wickerwaka/Arcade-IGSPGM_MiSTer/rtl/jt12/ver/jt12_mmr/verify_sorted.csv

0 | 0 0 | b | 69 | 1 | 0b | 0 | 1e | 02 | a | 8 | 1 | 7 / 0 | 0aa | 5 | 0 | 0 | 1 | 2
0 | 1 6 | 8 | 5e | 2 | 12 | 1 | 01 | 1a | 9 | 9 | 0 | 3 / 0 | 0d4 | 1 | 7 | 0 | 3 | 1
0 | 2 4 | 7 | 54 | 2 | 0d | 0 | 1e | 1e | 0 | f | 1 | 6 / 0 | 0ac | 0 | 5 | 2 | 3 | 2
0 | 4 6 | d | 76 | 3 | 06 | 0 | 17 | 03 | 9 | 5 | 1 | 0 / 0 | 0f2 | 2 | 4 | 2 | 2 | 3
0 | 5 7 | 7 | 5a | 3 | 1b | 0 | 0a | 1b | b | 1 | 1 | 4 / 0 | 01b | 3 | 3 | 1 | 1 | 5
0 | 6 5 | 6 | 2e | 2 | 14 | 0 | 1c | 1a | e | b | 1 | 3 / 0 | 010 | 7 | 7 | 3 | 3 | 5
1 | 0 7 | 9 | 63 | 2 | 14 | 1 | 0b | 0a | f | 1 | 0 | 4 / 0 | 0aa | 5 | 0 | 0 | 1 | 2
1 | 1 4 | 3 | 33 | 1 | 11 | 1 | 16 | 1a | b | 3 | 0 | 5 / 0 | 0d4 | 1 | 7 | 0 | 3 | 1
1 | 2 6 | 1 | 1f | 0 | 0e | 1 | 0f | 1b | 0 | 5 | 0 | 4 / 0 | 0ac | 0 | 5 | 2 | 3 | 2
1 | 4 2 | f | 49 | 0 | 02 | 0 | 18 | 09 | e | f | 0 | 3 / 0 | 0f2 | 2 | 4 | 2 | 2 | 3
1 | 5 4 | a | 1a | 2 | 14 | 1 | 1c | 11 | f | 7 | 1 | 2 / 0 | 01b | 3 | 3 | 1 | 1 | 5
1 | 6 3 | c | 66 | 1 | 01 | 1 | 0a | 06 | 0 | 0 | 0 | 5 / 0 | 010 | 7 | 7 | 3 | 3 | 5
2 | 0 2 | 9 | 32 | 1 | 01 | 0 | 0c | 05 | e | 9 | 1 | 6 / 0 | 0aa | 5 | 0 | 0 | 1 | 2
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
