wickerwaka/Arcade-IGSPGM_MiSTer/rtl/jt10_auto_ss.sv

///////////////////////////////////////////
// MODULE jt12_dout
module jt12_dout (
    // input             rst_n,
    input               clk,                      // CPU clock
    input               flag_A,
    input               flag_B,
    input               busy,
    input        [ 5:0] adpcma_flags,
    input               adpcmb_flag,
    input        [ 7:0] psg_dout,
    input        [ 1:0] addr,
    output reg   [ 7:0] dout,
    input               auto_ss_rd,
    input               auto_ss_wr,
    input        [31:0] auto_ss_data_in,
    input        [ 7:0] auto_ss_device_idx,
    input        [15:0] auto_ss_state_idx,
    input        [ 7:0] auto_ss_base_device_idx,
    output logic [31:0] auto_ss_data_out,
    output logic        auto_ss_ack

);
  wire device_match = (auto_ss_device_idx == auto_ss_base_device_idx);

  genvar auto_ss_idx;


  parameter use_ssg = 0, use_adpcm = 0;

  always @(posedge clk) begin
    begin
      casez (addr)
        2'b00: dout <= {busy, 5'd0, flag_B, flag_A};  // YM2203
        2'b01: dout <= (use_ssg == 1) ? psg_dout : {busy, 5'd0, flag_B, flag_A};
        2'b1?:
        dout <= (use_adpcm == 1) ? {adpcmb_flag, 1'b0, adpcma_flags} : {busy, 5'd0, flag_B, flag_A};
      endcase
    end
    if (auto_ss_wr && device_match) begin
      case (auto_ss_state_idx)
        0: begin
          dout <= auto_ss_data_in[7:0];
        end
        default: begin
        end
      endcase
    end
  end


  always_comb begin
    auto_ss_data_out = 32'h0;
    auto_ss_ack      = 1'b0;
    if (auto_ss_rd && device_match) begin
      case (auto_ss_state_idx)
        0: begin
          auto_ss_data_out[8-1:0] = dout;
          auto_ss_ack             = 1'b1;
        end
        default: begin
        end
      endcase
    end
  end



endmodule


///////////////////////////////////////////
// MODULE jt12_div
module jt12_div (
    input               rst,
    input               clk,
    input               cen  /* synthesis direct_enable */,
    input        [ 1:0] div_setting,
    output reg          clk_en,                              // after prescaler
    output reg          clk_en_2,                            // cen divided by 2
    output reg          clk_en_ssg,
    output reg          clk_en_666,                          // 666 kHz
    output reg          clk_en_111,                          // 111 kHz
    output reg          clk_en_55,
    input               auto_ss_rd,
    input               auto_ss_wr,
    input        [31:0] auto_ss_data_in,
    input        [ 7:0] auto_ss_device_idx,
    input        [15:0] auto_ss_state_idx,
    input        [ 7:0] auto_ss_base_device_idx,
    output logic [31:0] auto_ss_data_out,
    output logic        auto_ss_ack
    //  55 kHz
);
  wire device_match = (auto_ss_device_idx == auto_ss_base_device_idx);

  genvar auto_ss_idx;


  parameter use_ssg = 0;

  reg [3:0] opn_pres, opn_cnt = 4'd0;
  reg [2:0] ssg_pres, ssg_cnt = 3'd0;
  reg [4:0] adpcm_cnt666 = 5'd0;
  reg [2:0] adpcm_cnt111 = 3'd0, adpcm_cnt55 = 3'd0;
  reg cen_int, cen_ssg_int, cen_adpcm_int, cen_adpcm3_int;

  // prescaler values for FM
  // reset: 1/3
  // sel1/sel2
  //    0 0    1/3
  //    0 1    1/2
  //    1 0    1/6  
  //    1 1    1/2
  //
  // According to YM2608 document
  //                  FM      SSG   div[1:0]
  // reset value     1/6      1/4    10
  // 2D              1/6      1/4    10   | 10
  // 2D,2E           1/3      1/2    11   | 01
  // 2F              1/2      1/1    00   & 00
  //  

  always @(*) begin
    casez (div_setting)
      2'b0?: begin  // FM 1/2 - SSG 1/1
        opn_pres = 4'd2 - 4'd1;
        ssg_pres = 3'd0;
      end
      2'b10: begin  // FM 1/6 - SSG 1/4 (reset value. Fixed for YM2610)
        opn_pres = 4'd6 - 4'd1;
        ssg_pres = 3'd3;
      end
      2'b11: begin  // FM 1/3 - SSG 1/2
        opn_pres = 4'd3 - 4'd1;
        ssg_pres = 3'd1;
      end
    endcase  // div_setting
  end



  reg       cen_55_int;
  reg [1:0] div2 = 2'b0;

  always @(negedge clk) begin
    begin
      cen_int        <= opn_cnt == 4'd0;
      cen_ssg_int    <= ssg_cnt == 3'd0;
      cen_adpcm_int  <= adpcm_cnt666 == 5'd0;
      cen_adpcm3_int <= adpcm_cnt111 == 3'd0;
      cen_55_int     <= adpcm_cnt55 == 3'd0;

      clk_en         <= cen & cen_int;
      clk_en_2       <= cen && (div2 == 2'b00);
      clk_en_ssg     <= use_ssg ? (cen & cen_ssg_int) : 1'b0;
      clk_en_666     <= cen & cen_adpcm_int;
      clk_en_111     <= cen & cen_adpcm_int & cen_adpcm3_int;
      clk_en_55      <= cen & cen_adpcm_int & cen_adpcm3_int & cen_55_int;

    end
    if (auto_ss_wr && device_match) begin
      case (auto_ss_state_idx)
        0: begin
          cen_55_int     <= auto_ss_data_in[20];
          cen_adpcm3_int <= auto_ss_data_in[21];
          cen_adpcm_int  <= auto_ss_data_in[22];
          cen_int        <= auto_ss_data_in[23];
          cen_ssg_int    <= auto_ss_data_in[24];
          clk_en         <= auto_ss_data_in[25];
          clk_en_111     <= auto_ss_data_in[26];
          clk_en_2       <= auto_ss_data_in[27];
          clk_en_55      <= auto_ss_data_in[28];
          clk_en_666     <= auto_ss_data_in[29];
          clk_en_ssg     <= auto_ss_data_in[30];
        end
        default: begin
        end
      endcase
    end
  end



  // Div/2
  always @(posedge clk) begin

    if (cen) begin
      div2 <= div2 == 2'b10 ? 2'b00 : (div2 + 2'b01);
    end
    if (auto_ss_wr && device_match) begin
      case (auto_ss_state_idx)
        0: begin
          div2 <= auto_ss_data_in[19:18];
        end
        default: begin
        end
      endcase
    end
  end



  // OPN
  always @(posedge clk) begin

    if (cen) begin
      if (opn_cnt == opn_pres) begin
        opn_cnt <= 4'd0;
      end else opn_cnt <= opn_cnt + 4'd1;
    end
    if (auto_ss_wr && device_match) begin
      case (auto_ss_state_idx)
        0: begin
          opn_cnt <= auto_ss_data_in[8:5];
        end
        default: begin
        end
      endcase
    end
  end



  // SSG
  always @(posedge clk) begin

    if (cen) begin
      if (ssg_cnt == ssg_pres) begin
        ssg_cnt <= 3'd0;
      end else ssg_cnt <= ssg_cnt + 3'd1;
    end
    if (auto_ss_wr && device_match) begin
      case (auto_ss_state_idx)
        0: begin
          ssg_cnt <= auto_ss_data_in[11:9];
        end
        default: begin
        end
      endcase
    end
  end



  // ADPCM-A
  always @(posedge clk) begin

    if (cen) begin
      adpcm_cnt666 <= adpcm_cnt666 == 5'd11 ? 5'd0 : adpcm_cnt666 + 5'd1;
      if (adpcm_cnt666 == 5'd0) begin
        adpcm_cnt111 <= adpcm_cnt111 == 3'd5 ? 3'd0 : adpcm_cnt111 + 3'd1;
        if (adpcm_cnt111 == 3'd0) adpcm_cnt55 <= adpcm_cnt55 == 3'd1 ? 3'd0 : adpcm_cnt55 + 3'd1;
      end
    end
    if (auto_ss_wr && device_match) begin
      case (auto_ss_state_idx)
        0: begin
          adpcm_cnt666 <= auto_ss_data_in[4:0];
          adpcm_cnt111 <= auto_ss_data_in[14:12];
          adpcm_cnt55  <= auto_ss_data_in[17:15];
        end
        default: begin
        end
      endcase
    end
  end


  always_comb begin
    auto_ss_data_out = 32'h0;
    auto_ss_ack      = 1'b0;
    if (auto_ss_rd && device_match) begin
      case (auto_ss_state_idx)
        0: begin
          auto_ss_data_out[30:0] = {
            clk_en_ssg,
            clk_en_666,
            clk_en_55,
            clk_en_2,
            clk_en_111,
            clk_en,
            cen_ssg_int,
            cen_int,
            cen_adpcm_int,
            cen_adpcm3_int,
            cen_55_int,
            div2,
            adpcm_cnt55,
            adpcm_cnt111,
            ssg_cnt,
            opn_cnt,
            adpcm_cnt666
          };
          auto_ss_ack = 1'b1;
        end
        default: begin
        end
      endcase
    end
  end



endmodule


///////////////////////////////////////////
// MODULE jt12_sumch
module jt12_sumch (
    input      [4:0] chin,
    output reg [4:0] chout
);

  parameter num_ch = 6;

  reg [2:0] aux;

  always @(*) begin
    aux = chin[2:0] + 3'd1;
    if (num_ch == 6) begin
      chout[2:0] = aux[1:0] == 2'b11 ? aux + 3'd1 : aux;
      chout[4:3] = chin[2:0] == 3'd6 ? chin[4:3] + 2'd1 : chin[4:3];  // next operator
    end else begin  // 3 channels
      chout[2:0] = aux[1:0] == 2'b11 ? 3'd0 : aux;
      chout[4:3] = chin[2:0] == 3'd2 ? chin[4:3] + 2'd1 : chin[4:3];  // next operator
    end
  end

endmodule


///////////////////////////////////////////
// MODULE jt12_sh_rst
module jt12_sh_rst #(
    parameter width  = 5,
              stages = 32,
              rstval = 1'b0
) (
    input                    rst,
    input                    clk,
    input                    clk_en  /* synthesis direct_enable */,
    input        [width-1:0] din,
    output       [width-1:0] drop,
    input                    auto_ss_rd,
    input                    auto_ss_wr,
    input        [     31:0] auto_ss_data_in,
    input        [      7:0] auto_ss_device_idx,
    input        [     15:0] auto_ss_state_idx,
    input        [      7:0] auto_ss_base_device_idx,
    output logic [     31:0] auto_ss_data_out,
    output logic             auto_ss_ack


);
  wire device_match = (auto_ss_device_idx == auto_ss_base_device_idx);

  genvar auto_ss_idx;


  reg  [stages-1:0] bits                                    [width-1:0];
  wire [ width-1:0] din_mx = rst ? {width{rstval[0]}} : din;

  always @(posedge clk) begin
    begin
      if (clk_en) begin
        for (int i = 0; i < width; i = i + 1) begin
          bits[i] <= {bits[i][stages-2:0], din_mx[i]};
        end
      end
    end
    if (auto_ss_wr && device_match) begin
      if (auto_ss_state_idx < (width)) begin
        bits[auto_ss_state_idx] <= auto_ss_data_in[stages-1:0];
      end
    end
  end


  always_comb begin
    auto_ss_data_out = 32'h0;
    auto_ss_ack      = 1'b0;
    if (auto_ss_rd && device_match) begin
      if (auto_ss_state_idx < (width)) begin
        auto_ss_data_out[stages-1:0] = bits[auto_ss_state_idx];
        auto_ss_ack                  = 1'b1;
      end
    end
  end



  genvar i;
  generate
    for (i = 0; i < width; i = i + 1) begin : bit_shifter
      assign drop[i] = bits[i][stages-1];
    end
  endgenerate

endmodule


///////////////////////////////////////////
// MODULE jt12_kon
module jt12_kon (
    input       rst,
    input       clk,
    input       clk_en  /* synthesis direct_enable */,
    input [3:0] keyon_op,
    input [2:0] keyon_ch,
    input [1:0] next_op,
    input [2:0] next_ch,
    input       up_keyon,
    input       csm,
    // input            flag_A,
    input       overflow_A,

    output reg          keyon_I,
    input               auto_ss_rd,
    input               auto_ss_wr,
    input        [31:0] auto_ss_data_in,
    input        [ 7:0] auto_ss_device_idx,
    input        [15:0] auto_ss_state_idx,
    input        [ 7:0] auto_ss_base_device_idx,
    output logic [31:0] auto_ss_data_out,
    output logic        auto_ss_ack

);
  assign auto_ss_ack = auto_ss_local_ack | auto_ss_u_konch0_ack | auto_ss_u_konch1_ack | auto_ss_u_konch2_ack | auto_ss_u_konch3_ack;

  assign auto_ss_data_out = auto_ss_local_data_out | auto_ss_u_konch0_data_out | auto_ss_u_konch1_data_out | auto_ss_u_konch2_data_out | auto_ss_u_konch3_data_out;

  logic        auto_ss_local_ack;

  logic [31:0] auto_ss_local_data_out;

  wire         auto_ss_u_konch3_ack;

  wire  [31:0] auto_ss_u_konch3_data_out;

  wire         auto_ss_u_konch2_ack;

  wire  [31:0] auto_ss_u_konch2_data_out;

  wire         auto_ss_u_konch1_ack;

  wire  [31:0] auto_ss_u_konch1_data_out;

  wire         auto_ss_u_konch0_ack;

  wire  [31:0] auto_ss_u_konch0_data_out;

  wire         device_match = (auto_ss_device_idx == auto_ss_base_device_idx);

  genvar auto_ss_idx;


  parameter num_ch = 6;

  wire       csr_out;

  reg        overflow2;
  reg  [4:0] overflow_cycle;
  reg        up_keyon_reg;
  reg  [3:0] tkeyon_op;
  reg  [2:0] tkeyon_ch;


  generate
    if (num_ch == 6) begin
      // capture overflow signal so it lasts long enough
      always @(posedge clk) begin
        if (clk_en) begin
          if (overflow_A) begin
            overflow2      <= 1'b1;
            overflow_cycle <= {next_op, next_ch};
          end else begin
            if (overflow_cycle == {next_op, next_ch}) overflow2 <= 1'b0;
          end
        end
        if (auto_ss_wr && device_match) begin
          case (auto_ss_state_idx)
            0: begin
              overflow_cycle <= auto_ss_data_in[4:0];
              overflow2      <= auto_ss_data_in[12];
            end
            default: begin
            end
          endcase
        end
      end



      always @(posedge clk) begin
        if (clk_en) keyon_I <= (csm && next_ch == 3'd2 && overflow2) || csr_out;
        if (auto_ss_wr && device_match) begin
          case (auto_ss_state_idx)
            0: begin
              keyon_I <= auto_ss_data_in[15];
              keyon_I <= auto_ss_data_in[15];
            end
            default: begin
            end
          endcase
        end
      end



      wire key_upnow;

      assign key_upnow = up_keyon_reg && (tkeyon_ch == next_ch) && (next_op == 2'd3);

      always @(posedge clk) begin
        if (clk_en) begin
          if (rst) up_keyon_reg <= 1'b0;
          if (up_keyon) begin
            up_keyon_reg <= 1'b1;
            tkeyon_op    <= keyon_op;
            tkeyon_ch    <= keyon_ch;
          end else if (key_upnow) up_keyon_reg <= 1'b0;
        end
        if (auto_ss_wr && device_match) begin
          case (auto_ss_state_idx)
            0: begin
              tkeyon_op    <= auto_ss_data_in[8:5];
              tkeyon_ch    <= auto_ss_data_in[11:9];
              up_keyon_reg <= auto_ss_data_in[14];
            end
            default: begin
            end
          endcase
        end
      end




      wire middle1;
      wire middle2;
      wire middle3;
      wire din = key_upnow ? tkeyon_op[3] : csr_out;
      wire mid_din2 = key_upnow ? tkeyon_op[1] : middle1;
      wire mid_din3 = key_upnow ? tkeyon_op[2] : middle2;
      wire mid_din4 = key_upnow ? tkeyon_op[0] : middle3;

      jt12_sh_rst #(
          .width (1),
          .stages(6),
          .rstval(1'b0)
      ) u_konch0 (
          .clk                    (clk),
          .clk_en                 (clk_en),
          .rst                    (rst),
          .din                    (din),
          .drop                   (middle1),
          .auto_ss_rd             (auto_ss_rd),
          .auto_ss_wr             (auto_ss_wr),
          .auto_ss_data_in        (auto_ss_data_in),
          .auto_ss_device_idx     (auto_ss_device_idx),
          .auto_ss_state_idx      (auto_ss_state_idx),
          .auto_ss_base_device_idx(auto_ss_base_device_idx + 1),
          .auto_ss_data_out       (auto_ss_u_konch0_data_out),
          .auto_ss_ack            (auto_ss_u_konch0_ack)

      );

      jt12_sh_rst #(
          .width (1),
          .stages(6),
          .rstval(1'b0)
      ) u_konch1 (
          .clk                    (clk),
          .clk_en                 (clk_en),
          .rst                    (rst),
          .din                    (mid_din2),
          .drop                   (middle2),
          .auto_ss_rd             (auto_ss_rd),
          .auto_ss_wr             (auto_ss_wr),
          .auto_ss_data_in        (auto_ss_data_in),
          .auto_ss_device_idx     (auto_ss_device_idx),
          .auto_ss_state_idx      (auto_ss_state_idx),
          .auto_ss_base_device_idx(auto_ss_base_device_idx + 2),
          .auto_ss_data_out       (auto_ss_u_konch1_data_out),
          .auto_ss_ack            (auto_ss_u_konch1_ack)

      );

      jt12_sh_rst #(
          .width (1),
          .stages(6),
          .rstval(1'b0)
      ) u_konch2 (
          .clk                    (clk),
          .clk_en                 (clk_en),
          .rst                    (rst),
          .din                    (mid_din3),
          .drop                   (middle3),
          .auto_ss_rd             (auto_ss_rd),
          .auto_ss_wr             (auto_ss_wr),
          .auto_ss_data_in        (auto_ss_data_in),
          .auto_ss_device_idx     (auto_ss_device_idx),
          .auto_ss_state_idx      (auto_ss_state_idx),
          .auto_ss_base_device_idx(auto_ss_base_device_idx + 3),
          .auto_ss_data_out       (auto_ss_u_konch2_data_out),
          .auto_ss_ack            (auto_ss_u_konch2_ack)

      );

      jt12_sh_rst #(
          .width (1),
          .stages(6),
          .rstval(1'b0)
      ) u_konch3 (
          .clk                    (clk),
          .clk_en                 (clk_en),
          .rst                    (rst),
          .din                    (mid_din4),
          .drop                   (csr_out),
          .auto_ss_rd             (auto_ss_rd),
          .auto_ss_wr             (auto_ss_wr),
          .auto_ss_data_in        (auto_ss_data_in),
          .auto_ss_device_idx     (auto_ss_device_idx),
          .auto_ss_state_idx      (auto_ss_state_idx),
          .auto_ss_base_device_idx(auto_ss_base_device_idx + 4),
          .auto_ss_data_out       (auto_ss_u_konch3_data_out),
          .auto_ss_ack            (auto_ss_u_konch3_ack)

      );
    end else begin  // 3 channels
      reg       din;
      reg [3:0] next_op_hot;

      always @(*) begin
        case (next_op)
          2'd0: next_op_hot = 4'b0001;  // S1
          2'd1: next_op_hot = 4'b0100;  // S3
          2'd2: next_op_hot = 4'b0010;  // S2
          2'd3: next_op_hot = 4'b1000;  // S4
        endcase
        din = keyon_ch[1:0] == next_ch[1:0] && up_keyon ? |(keyon_op & next_op_hot) : csr_out;
      end

      always @(posedge clk) begin
        if (clk_en) keyon_I <= csr_out;
        if (auto_ss_wr && device_match) begin
          case (auto_ss_state_idx)
            0: begin
              keyon_I <= auto_ss_data_in[15];
              keyon_I <= auto_ss_data_in[15];
            end
            default: begin
            end
          endcase
        end
      end


      always_comb begin
        auto_ss_local_data_out = 32'h0;
        auto_ss_local_ack      = 1'b0;
        if (auto_ss_rd && device_match) begin
          case (auto_ss_state_idx)
            0: begin
              auto_ss_local_data_out[15:0] = {
                keyon_I, keyon_I, up_keyon_reg, overflow2, tkeyon_ch, tkeyon_op, overflow_cycle
              };
              auto_ss_local_ack = 1'b1;
            end
            default: begin
            end
          endcase
        end
      end

      // No CSM for YM2203

      jt12_sh_rst #(
          .width (1),
          .stages(12),
          .rstval(1'b0)
      ) u_konch1 (
          .clk                    (clk),
          .clk_en                 (clk_en),
          .rst                    (rst),
          .din                    (din),
          .drop                   (csr_out),
          .auto_ss_rd             (auto_ss_rd),
          .auto_ss_wr             (auto_ss_wr),
          .auto_ss_data_in        (auto_ss_data_in),
          .auto_ss_device_idx     (auto_ss_device_idx),
          .auto_ss_state_idx      (auto_ss_state_idx),
          .auto_ss_base_device_idx(auto_ss_base_device_idx + 5),
          .auto_ss_data_out       (auto_ss_u_konch1_data_out),
          .auto_ss_ack            (auto_ss_u_konch1_ack)

      );
    end
  endgenerate


endmodule


///////////////////////////////////////////
// MODULE jt12_mod
module jt12_mod (
    input s1_enters,
    input s2_enters,
    input s3_enters,
    input s4_enters,

    input [2:0] alg_I,

    output reg xuse_prevprev1,
    output reg xuse_internal,
    output reg yuse_internal,
    output reg xuse_prev2,
    output reg yuse_prev1,
    output reg yuse_prev2
);

  parameter num_ch = 6;

  reg [7:0] alg_hot;

  always @(*) begin
    case (alg_I)
      3'd0: alg_hot = 8'h1;  // D0
      3'd1: alg_hot = 8'h2;  // D1
      3'd2: alg_hot = 8'h4;  // D2
      3'd3: alg_hot = 8'h8;  // D3
      3'd4: alg_hot = 8'h10;  // D4
      3'd5: alg_hot = 8'h20;  // D5
      3'd6: alg_hot = 8'h40;  // D6
      3'd7: alg_hot = 8'h80;  // D7
    endcase
  end

  // prev2 cannot modulate with prevprev1 at the same time
  // x = prev2, prevprev1, internal_x
  // y = prev1, internal_y

  generate
    if (num_ch == 6) begin
      always @(*) begin
        xuse_prevprev1 = s1_enters | (s3_enters & alg_hot[5]);
        xuse_prev2 = (s3_enters & (|alg_hot[2:0])) | (s4_enters & alg_hot[3]);
        xuse_internal = s4_enters & alg_hot[2];
        yuse_internal = s4_enters & (|{alg_hot[4:3], alg_hot[1:0]});
        yuse_prev1 = s1_enters | (s3_enters&alg_hot[1]) |
                (s2_enters&(|{alg_hot[6:3],alg_hot[0]}) )|
                (s4_enters&(|{alg_hot[5],alg_hot[2]}));
        yuse_prev2 = 1'b0;  // unused for 6 channels
      end
    end else begin
      reg [2:0] xuse_s4, xuse_s3, xuse_s2, xuse_s1;
      reg [2:0] yuse_s4, yuse_s3, yuse_s2, yuse_s1;
      always @(*) begin  // 3 ch
        // S1
        {xuse_s1, yuse_s1} = {3'b001, 3'b100};
        // S2
        casez (1'b1)
          // S2 modulated by S1
          alg_hot[6], alg_hot[5], alg_hot[4], alg_hot[3], alg_hot[0]:
          {xuse_s2, yuse_s2} = {3'b000, 3'b100};  // prev1
          default: {xuse_s2, yuse_s2} = 6'd0;
        endcase
        // S3
        casez (1'b1)
          // S3 modulated by S1
          alg_hot[5]: {xuse_s3, yuse_s3} = {3'b000, 3'b100};  // prev1
          // S3 modulated by S2
          alg_hot[2], alg_hot[0]: {xuse_s3, yuse_s3} = {3'b000, 3'b010};  // prev2
          // S3 modulated by S2+S1
          alg_hot[1]: {xuse_s3, yuse_s3} = {3'b010, 3'b100};  // prev2 + prev1                   
          default: {xuse_s3, yuse_s3} = 6'd0;
        endcase
        // S4
        casez (1'b1)
          // S4 modulated by S1
          alg_hot[5]: {xuse_s4, yuse_s4} = {3'b000, 3'b100};  // prev1
          // S4 modulated by S3
          alg_hot[4], alg_hot[1], alg_hot[0]: {xuse_s4, yuse_s4} = {3'b100, 3'b000};  // prevprev1
          // S4 modulated by S3+S2
          alg_hot[3]: {xuse_s4, yuse_s4} = {3'b100, 3'b010};  // prevprev1+prev2                    
          // S4 modulated by S3+S1
          alg_hot[2]: {xuse_s4, yuse_s4} = {3'b100, 3'b100};  // prevprev1+prev1
          default: {xuse_s4, yuse_s4} = 6'd0;
        endcase
        case ({
          s4_enters, s3_enters, s2_enters, s1_enters
        })
          4'b1000: begin
            {xuse_prevprev1, xuse_prev2, xuse_internal} = xuse_s4;
            {yuse_prev1, yuse_prev2, yuse_internal}     = yuse_s4;
          end
          4'b0100: begin
            {xuse_prevprev1, xuse_prev2, xuse_internal} = xuse_s3;
            {yuse_prev1, yuse_prev2, yuse_internal}     = yuse_s3;
          end
          4'b0010: begin
            {xuse_prevprev1, xuse_prev2, xuse_internal} = xuse_s2;
            {yuse_prev1, yuse_prev2, yuse_internal}     = yuse_s2;
          end
          4'b0001: begin
            {xuse_prevprev1, xuse_prev2, xuse_internal} = xuse_s1;
            {yuse_prev1, yuse_prev2, yuse_internal}     = yuse_s1;
          end
          default: begin
            {xuse_prevprev1, xuse_prev2, xuse_internal} = 3'b0;
            {yuse_prev1, yuse_prev2, yuse_internal}     = 3'b0;
          end
        endcase
      end
    end
  endgenerate

  // Control signals for simulation: should be 2'b0 or 2'b1
  // wire [1:0] xusage = xuse_prevprev1+xuse_prev2+xuse_internal;
  // wire [1:0] yusage = yuse_prev1+yuse_internal;
  // 
  // always @(xusage,yusage)
  //     if( xusage>2'b1 || yusage>2'b1 ) begin
  //         $display("ERROR: x/y over use in jt12_mod");
  //         $finish;
  //     end

endmodule


///////////////////////////////////////////
// MODULE jt12_reg_ch
module jt12_reg_ch (
    input       rst,
    input       clk,
    input       cen,
    input [7:0] din,

    input [2:0] up_ch,
    input [5:0] latch_fnum,
    input       up_fnumlo,
    input       up_alg,
    input       up_pms,

    input        [ 2:0] ch,                       // next active channel
    output reg   [ 2:0] block,
    output reg   [10:0] fnum,
    output reg   [ 2:0] fb,
    output reg   [ 2:0] alg,
    output reg   [ 1:0] rl,
    output reg   [ 1:0] ams_IV,
    output reg   [ 2:0] pms,
    input               auto_ss_rd,
    input               auto_ss_wr,
    input        [31:0] auto_ss_data_in,
    input        [ 7:0] auto_ss_device_idx,
    input        [15:0] auto_ss_state_idx,
    input        [ 7:0] auto_ss_base_device_idx,
    output logic [31:0] auto_ss_data_out,
    output logic        auto_ss_ack

);
  wire device_match = (auto_ss_device_idx == auto_ss_base_device_idx);

  genvar auto_ss_idx;


  parameter NUM_CH = 6;
  localparam M = NUM_CH == 3 ? 2 : 3;

  reg [ 2:0] reg_block[0:NUM_CH-1];
  reg [10:0] reg_fnum [0:NUM_CH-1];
  reg [ 2:0] reg_fb   [0:NUM_CH-1];
  reg [ 2:0] reg_alg  [0:NUM_CH-1];
  reg [ 1:0] reg_rl   [0:NUM_CH-1];
  reg [ 1:0] reg_ams  [0:NUM_CH-1];
  reg [ 2:0] reg_pms  [0:NUM_CH-1];
  reg [ 2:0] ch_IV;

  wire [M-1:0] ch_sel, out_sel;

  function [M-1:0] chtr(input [2:0] chin);
    reg [2:0] aux;
    begin
      aux  = chin[M-1] ? {1'b0, chin[1:0]} + 3'd3 :  // upper channels
{1'b0, chin[1:0]};  // lower
      chtr = NUM_CH == 3 ? chin[M-1:0] : aux[M-1:0];

    end
  endfunction

  assign ch_sel  = chtr(up_ch);
  assign out_sel = chtr(ch);

  integer i;
  /* verilator lint_off WIDTHEXPAND */
  always @* begin
    ch_IV = ch;
    if (NUM_CH == 6)
      case (out_sel)
        0: ch_IV = 3;
        1: ch_IV = 4;
        2: ch_IV = 5;
        3: ch_IV = 0;
        4: ch_IV = 1;
        5: ch_IV = 2;
        default: ch_IV = 0;
      endcase
  end
  /* verilator lint_on WIDTHEXPAND */

  always @(posedge clk) begin
    if (cen) begin
      block  <= reg_block[out_sel];
      fnum   <= reg_fnum[out_sel];
      fb     <= reg_fb[out_sel];
      alg    <= reg_alg[out_sel];
      rl     <= reg_rl[out_sel];
      ams_IV <= reg_ams[ch_IV[M-1:0]];
      pms    <= reg_pms[out_sel];
      if (NUM_CH == 3) rl <= 3;  // YM2203 has no stereo output
    end
    if (auto_ss_wr && device_match) begin
      case (auto_ss_state_idx)
        0: begin
          fnum   <= auto_ss_data_in[10:0];
          alg    <= auto_ss_data_in[13:11];
          block  <= auto_ss_data_in[16:14];
          fb     <= auto_ss_data_in[19:17];
          pms    <= auto_ss_data_in[22:20];
          ams_IV <= auto_ss_data_in[24:23];
          rl     <= auto_ss_data_in[26:25];
        end
        default: begin
        end
      endcase
    end
  end



  always @(posedge clk, posedge rst) begin
    if (rst)
      for (i = 0; i < NUM_CH; i = i + 1) begin
        reg_block[i] <= 0;
        reg_fnum[i]  <= 0;
        reg_fb[i]    <= 0;
        reg_alg[i]   <= 0;
        reg_rl[i]    <= 3;
        reg_ams[i]   <= 0;
        reg_pms[i]   <= 0;
      end
    else if (auto_ss_wr && device_match) begin
      if (auto_ss_state_idx >= (1) && auto_ss_state_idx < (NUM_CH + 1)) begin
        reg_alg[auto_ss_state_idx-1] <= auto_ss_data_in[2:0];
      end
      if (auto_ss_state_idx >= (NUM_CH + 1) && auto_ss_state_idx < (2 * NUM_CH + 1)) begin
        reg_ams[-NUM_CH+auto_ss_state_idx-1] <= auto_ss_data_in[1:0];
      end
      if (auto_ss_state_idx >= (2 * NUM_CH + 1) && auto_ss_state_idx < (3 * NUM_CH + 1)) begin
        reg_block[-2*NUM_CH+auto_ss_state_idx-1] <= auto_ss_data_in[2:0];
      end
      if (auto_ss_state_idx >= (3 * NUM_CH + 1) && auto_ss_state_idx < (4 * NUM_CH + 1)) begin
        reg_fb[-3*NUM_CH+auto_ss_state_idx-1] <= auto_ss_data_in[2:0];
      end
      if (auto_ss_state_idx >= (4 * NUM_CH + 1) && auto_ss_state_idx < (5 * NUM_CH + 1)) begin
        reg_fnum[-4*NUM_CH+auto_ss_state_idx-1] <= auto_ss_data_in[10:0];
      end
      if (auto_ss_state_idx >= (5 * NUM_CH + 1) && auto_ss_state_idx < (6 * NUM_CH + 1)) begin
        reg_pms[-5*NUM_CH+auto_ss_state_idx-1] <= auto_ss_data_in[2:0];
      end
      if (auto_ss_state_idx >= (6 * NUM_CH + 1) && auto_ss_state_idx < (7 * NUM_CH + 1)) begin
        reg_rl[-6*NUM_CH+auto_ss_state_idx-1] <= auto_ss_data_in[1:0];
      end
    end else begin
      i = 0;  // prevents latch warning in Quartus
      if (up_fnumlo) {reg_block[ch_sel], reg_fnum[ch_sel]} <= {latch_fnum, din};
      if (up_alg) begin
        reg_fb[ch_sel]  <= din[5:3];
        reg_alg[ch_sel] <= din[2:0];
      end
      if (up_pms) begin
        reg_rl[ch_sel]  <= din[7:6];
        reg_ams[ch_sel] <= din[5:4];
        reg_pms[ch_sel] <= din[2:0];
      end
    end
  end
  always_comb begin
    auto_ss_data_out = 32'h0;
    auto_ss_ack      = 1'b0;
    if (auto_ss_rd && device_match) begin
      case (auto_ss_state_idx)
        0: begin
          auto_ss_data_out[26:0] = {rl, ams_IV, pms, fb, block, alg, fnum};
          auto_ss_ack            = 1'b1;
        end
        default: begin
          if (auto_ss_state_idx >= (1) && auto_ss_state_idx < (NUM_CH + 1)) begin
            auto_ss_data_out[3-1:0] = reg_alg[auto_ss_state_idx-1];
            auto_ss_ack             = 1'b1;
          end
          if (auto_ss_state_idx >= (NUM_CH + 1) && auto_ss_state_idx < (2 * NUM_CH + 1)) begin
            auto_ss_data_out[2-1:0] = reg_ams[-NUM_CH+auto_ss_state_idx-1];
            auto_ss_ack             = 1'b1;
          end
          if (auto_ss_state_idx >= (2 * NUM_CH + 1) && auto_ss_state_idx < (3 * NUM_CH + 1)) begin
            auto_ss_data_out[3-1:0] = reg_block[-2*NUM_CH+auto_ss_state_idx-1];
            auto_ss_ack             = 1'b1;
          end
          if (auto_ss_state_idx >= (3 * NUM_CH + 1) && auto_ss_state_idx < (4 * NUM_CH + 1)) begin
            auto_ss_data_out[3-1:0] = reg_fb[-3*NUM_CH+auto_ss_state_idx-1];
            auto_ss_ack             = 1'b1;
          end
          if (auto_ss_state_idx >= (4 * NUM_CH + 1) && auto_ss_state_idx < (5 * NUM_CH + 1)) begin
            auto_ss_data_out[11-1:0] = reg_fnum[-4*NUM_CH+auto_ss_state_idx-1];
            auto_ss_ack              = 1'b1;
          end
          if (auto_ss_state_idx >= (5 * NUM_CH + 1) && auto_ss_state_idx < (6 * NUM_CH + 1)) begin
            auto_ss_data_out[3-1:0] = reg_pms[-5*NUM_CH+auto_ss_state_idx-1];
            auto_ss_ack             = 1'b1;
          end
          if (auto_ss_state_idx >= (6 * NUM_CH + 1) && auto_ss_state_idx < (7 * NUM_CH + 1)) begin
            auto_ss_data_out[2-1:0] = reg_rl[-6*NUM_CH+auto_ss_state_idx-1];
            auto_ss_ack             = 1'b1;
          end
        end
      endcase
    end
  end



endmodule


///////////////////////////////////////////
// MODULE jt12_csr
module jt12_csr (  // Circular Shift Register + input mux
    input         rst,
    input         clk,
    input         clk_en  /* synthesis direct_enable */,
    input  [ 7:0] din,
    input  [43:0] shift_in,
    output [43:0] shift_out,

    input               up_tl,
    input               up_dt1,
    input               up_ks_ar,
    input               up_amen_dr,
    input               up_sr,
    input               up_sl_rr,
    input               up_ssgeg,
    input               update_op_I,
    input               update_op_II,
    input               update_op_IV,
    input               auto_ss_rd,
    input               auto_ss_wr,
    input        [31:0] auto_ss_data_in,
    input        [ 7:0] auto_ss_device_idx,
    input        [15:0] auto_ss_state_idx,
    input        [ 7:0] auto_ss_base_device_idx,
    output logic [31:0] auto_ss_data_out,
    output logic        auto_ss_ack

);
  assign auto_ss_ack      = auto_ss_u_regch_ack;

  assign auto_ss_data_out = auto_ss_u_regch_data_out;

  wire        auto_ss_u_regch_ack;

  wire [31:0] auto_ss_u_regch_data_out;

  wire        device_match = (auto_ss_device_idx == auto_ss_base_device_idx);

  genvar auto_ss_idx;


  localparam regop_width = 44;

  reg [regop_width-1:0] regop_in;

  jt12_sh_rst #(
      .width (regop_width),
      .stages(12)
  ) u_regch (
      .clk                    (clk),
      .clk_en                 (clk_en),
      .rst                    (rst),
      .din                    (regop_in),
      .drop                   (shift_out),
      .auto_ss_rd             (auto_ss_rd),
      .auto_ss_wr             (auto_ss_wr),
      .auto_ss_data_in        (auto_ss_data_in),
      .auto_ss_device_idx     (auto_ss_device_idx),
      .auto_ss_state_idx      (auto_ss_state_idx),
      .auto_ss_base_device_idx(auto_ss_base_device_idx + 1),
      .auto_ss_data_out       (auto_ss_u_regch_data_out),
      .auto_ss_ack            (auto_ss_u_regch_ack)

  );

  wire up_tl_op = up_tl & update_op_IV;
  wire up_dt1_op = up_dt1 & update_op_I;
  wire up_mul_op = up_dt1 & update_op_II;
  wire up_ks_op = up_ks_ar & update_op_II;
  wire up_ar_op = up_ks_ar & update_op_I;
  wire up_amen_op = up_amen_dr & update_op_IV;
  wire up_dr_op = up_amen_dr & update_op_I;
  wire up_sr_op = up_sr & update_op_I;
  wire up_sl_op = up_sl_rr & update_op_I;
  wire up_rr_op = up_sl_rr & update_op_I;
  wire up_ssg_op = up_ssgeg & update_op_I;

  always @(*)
    regop_in = {
      up_tl_op ? din[6:0] : shift_in[43:37],  // 7 
      up_dt1_op ? din[6:4] : shift_in[36:34],  // 3 
      up_mul_op ? din[3:0] : shift_in[33:30],  // 4 
      up_ks_op ? din[7:6] : shift_in[29:28],  // 2 
      up_ar_op ? din[4:0] : shift_in[27:23],  // 5 
      up_amen_op ? din[7] : shift_in[22],  // 1 
      up_dr_op ? din[4:0] : shift_in[21:17],  // 5 
      up_sr_op ? din[4:0] : shift_in[16:12],  // 5 
      up_sl_op ? din[7:4] : shift_in[11:8],  // 4 
      up_rr_op ? din[3:0] : shift_in[7:4],  // 4 
      up_ssg_op ? din[3:0] : shift_in[3:0]  // 4 
    };

endmodule


///////////////////////////////////////////
// MODULE jt12_reg
module jt12_reg (
    input rst,
    input clk,
    input clk_en  /* synthesis direct_enable */,

    input [2:0] ch,  // channel to update
    input [1:0] op,

    input csm,
    input flag_A,
    input overflow_A,

    // channel udpates
    input [2:0] ch_sel,
    input [7:0] ch_din,
    input       up_alg,
    input       up_fnumlo,
    // operator updates
    input [7:0] din,
    input       up_keyon,
    input       up_pms,
    input       up_dt1,
    input       up_tl,
    input       up_ks_ar,
    input       up_amen_dr,
    input       up_sr,
    input       up_sl_rr,
    input       up_ssgeg,

    output reg       ch6op,   // 1 when the operator belongs to CH6
    output reg [2:0] cur_ch,
    output reg [1:0] cur_op,

    // CH3 Effect-mode operation
    input             effect,
    input      [10:0] fnum_ch3op2,
    input      [10:0] fnum_ch3op3,
    input      [10:0] fnum_ch3op1,
    input      [ 2:0] block_ch3op2,
    input      [ 2:0] block_ch3op3,
    input      [ 2:0] block_ch3op1,
    input      [ 5:0] latch_fnum,
    // Pipeline order
    output reg        zero,
    output            s1_enters,
    output            s2_enters,
    output            s3_enters,
    output            s4_enters,

    // Operator
    output xuse_prevprev1,
    output xuse_internal,
    output yuse_internal,
    output xuse_prev2,
    output yuse_prev1,
    output yuse_prev2,

    // PG
    output     [10:0] fnum_I,
    output     [ 2:0] block_I,
    // channel configuration
    output     [ 1:0] rl,
    output reg [ 2:0] fb_II,
    output     [ 2:0] alg_I,
    // Operator multiplying
    output     [ 3:0] mul_II,
    // Operator detuning
    output     [ 2:0] dt1_I,

    // EG
    output [4:0] ar_I,      // attack  rate
    output [4:0] d1r_I,     // decay   rate
    output [4:0] d2r_I,     // sustain rate
    output [3:0] rr_I,      // release rate
    output [3:0] sl_I,      // sustain level
    output [1:0] ks_II,     // key scale
    output       ssg_en_I,
    output [2:0] ssg_eg_I,
    output [6:0] tl_IV,
    output [2:0] pms_I,
    output [1:0] ams_IV,
    output       amsen_IV,

    // envelope operation
    output              keyon_I,
    input               auto_ss_rd,
    input               auto_ss_wr,
    input        [31:0] auto_ss_data_in,
    input        [ 7:0] auto_ss_device_idx,
    input        [15:0] auto_ss_state_idx,
    input        [ 7:0] auto_ss_base_device_idx,
    output logic [31:0] auto_ss_data_out,
    output logic        auto_ss_ack

);
  assign auto_ss_ack = auto_ss_local_ack | auto_ss_u_kon_ack | auto_ss_u_regch_ack | auto_ss_u_csr0_ack | auto_ss_u_csr1_ack;

  assign auto_ss_data_out = auto_ss_local_data_out | auto_ss_u_kon_data_out | auto_ss_u_regch_data_out | auto_ss_u_csr0_data_out | auto_ss_u_csr1_data_out;

  logic        auto_ss_local_ack;

  logic [31:0] auto_ss_local_data_out;

  wire         auto_ss_u_csr1_ack;

  wire  [31:0] auto_ss_u_csr1_data_out;

  wire         auto_ss_u_csr0_ack;

  wire  [31:0] auto_ss_u_csr0_data_out;

  wire         auto_ss_u_regch_ack;

  wire  [31:0] auto_ss_u_regch_data_out;

  wire         auto_ss_u_kon_ack;

  wire  [31:0] auto_ss_u_kon_data_out;

  wire         device_match = (auto_ss_device_idx == auto_ss_base_device_idx);

  genvar auto_ss_idx;


  parameter num_ch = 6;  // Use only 3 (YM2203/YM2610) or 6 (YM2612/YM2608)


  reg [1:0] next_op;
  reg [2:0] next_ch;
  reg       last;



  assign s1_enters = cur_op == 2'b00;
  assign s3_enters = cur_op == 2'b01;
  assign s2_enters = cur_op == 2'b10;
  assign s4_enters = cur_op == 2'b11;

  wire [4:0] next = {next_op, next_ch};
  wire [4:0] cur = {cur_op, cur_ch};

  wire [2:0] fb_I;

  always @(posedge clk) begin
    if (clk_en) begin
      fb_II <= fb_I;
      ch6op <= next_ch == 3'd6;
    end
    if (auto_ss_wr && device_match) begin
      case (auto_ss_state_idx)
        0: begin
          fb_II <= auto_ss_data_in[2:0];
          ch6op <= auto_ss_data_in[5];
        end
        default: begin
        end
      endcase
    end
  end



  // FNUM and BLOCK
  wire [10:0] fnum_I_raw;
  wire [ 2:0] block_I_raw;
  wire        effect_on = effect && (cur_ch == 3'd2);
  wire        effect_on_s1 = effect_on && (cur_op == 2'd0);
  wire        effect_on_s3 = effect_on && (cur_op == 2'd1);
  wire        effect_on_s2 = effect_on && (cur_op == 2'd2);
  wire        noeffect = ~|{effect_on_s1, effect_on_s3, effect_on_s2};
  assign fnum_I = ( {11{effect_on_s1}} & fnum_ch3op1 ) |
                ( {11{effect_on_s2}} & fnum_ch3op2 ) |
                ( {11{effect_on_s3}} & fnum_ch3op3 ) |
                ( {11{noeffect}}     & fnum_I_raw  );

  assign block_I =( {3{effect_on_s1}} & block_ch3op1 ) |
                ( {3{effect_on_s2}} & block_ch3op2 ) |
                ( {3{effect_on_s3}} & block_ch3op3 ) |
                ( {3{noeffect}}  & block_I_raw  );

  wire [4:0] req_opch_I = {op, ch};
  wire [4:0] req_opch_II, req_opch_III, req_opch_IV, req_opch_V;  //, req_opch_VI;

  jt12_sumch #(
      .num_ch(num_ch)
  ) u_opch_II (
      .chin (req_opch_I),
      .chout(req_opch_II)
  );
  jt12_sumch #(
      .num_ch(num_ch)
  ) u_opch_III (
      .chin (req_opch_II),
      .chout(req_opch_III)
  );
  jt12_sumch #(
      .num_ch(num_ch)
  ) u_opch_IV (
      .chin (req_opch_III),
      .chout(req_opch_IV)
  );
  jt12_sumch #(
      .num_ch(num_ch)
  ) u_opch_V (
      .chin (req_opch_IV),
      .chout(req_opch_V)
  );
  // jt12_sumch #(.num_ch(num_ch)) u_opch_VI ( .chin(req_opch_V  ), .chout(req_opch_VI)  );

  wire       update_op_I = cur == req_opch_I;
  wire       update_op_II = cur == req_opch_II;
  // wire update_op_III= cur == req_opch_III;
  wire       update_op_IV = cur == req_opch_IV;
  // wire update_op_V  = cur == req_opch_V;
  // wire update_op_VI = cur == opch_VI;
  // wire [2:0] op_plus1 = op+2'd1;
  // wire update_op_VII= cur == { op_plus1[1:0], ch };

  // key on/off
  wire [3:0] keyon_op = din[7:4];
  wire [2:0] keyon_ch = din[2:0];

  always @(*) begin
    // next = cur==5'd23 ? 5'd0 : cur +1'b1;
    if (num_ch == 6) begin
      next_op = cur_ch == 3'd6 ? cur_op + 1'b1 : cur_op;
      next_ch = cur_ch[1:0] == 2'b10 ? cur_ch + 2'd2 : cur_ch + 1'd1;
    end else begin  // 3 channels
      next_op = cur_ch == 3'd2 ? cur_op + 1'b1 : cur_op;
      next_ch = cur_ch[1:0] == 2'b10 ? 3'd0 : cur_ch + 1'd1;
    end
  end

  always @(posedge clk) begin
    begin : up_counter
      if (clk_en) begin
        {cur_op, cur_ch} <= {next_op, next_ch};
        zero             <= next == 5'd0;
      end
    end
    if (auto_ss_wr && device_match) begin
      case (auto_ss_state_idx)
        0: begin
          cur_op <= auto_ss_data_in[4:3];
          zero   <= auto_ss_data_in[6];
        end
        default: begin
        end
      endcase
    end
  end


  always_comb begin
    auto_ss_local_data_out = 32'h0;
    auto_ss_local_ack      = 1'b0;
    if (auto_ss_rd && device_match) begin
      case (auto_ss_state_idx)
        0: begin
          auto_ss_local_data_out[6:0] = {zero, ch6op, cur_op, fb_II};
          auto_ss_local_ack           = 1'b1;
        end
        default: begin
        end
      endcase
    end
  end




  jt12_kon #(
      .num_ch(num_ch)
  ) u_kon (
      .rst       (rst),
      .clk       (clk),
      .clk_en    (clk_en),
      .keyon_op  (keyon_op),
      .keyon_ch  (keyon_ch),
      .next_op   (next_op),
      .next_ch   (next_ch),
      .up_keyon  (up_keyon),
      .csm       (csm),
      // .flag_A      ( flag_A    ),
      .overflow_A(overflow_A),

      .keyon_I                (keyon_I),
      .auto_ss_rd             (auto_ss_rd),
      .auto_ss_wr             (auto_ss_wr),
      .auto_ss_data_in        (auto_ss_data_in),
      .auto_ss_device_idx     (auto_ss_device_idx),
      .auto_ss_state_idx      (auto_ss_state_idx),
      .auto_ss_base_device_idx(auto_ss_base_device_idx + 1),
      .auto_ss_data_out       (auto_ss_u_kon_data_out),
      .auto_ss_ack            (auto_ss_u_kon_ack)

  );

  jt12_mod #(
      .num_ch(num_ch)
  ) u_mod (
      .alg_I    (alg_I),
      .s1_enters(s1_enters),
      .s3_enters(s3_enters),
      .s2_enters(s2_enters),
      .s4_enters(s4_enters),

      .xuse_prevprev1(xuse_prevprev1),
      .xuse_internal (xuse_internal),
      .yuse_internal (yuse_internal),
      .xuse_prev2    (xuse_prev2),
      .yuse_prev1    (yuse_prev1),
      .yuse_prev2    (yuse_prev2)
  );

  wire [43:0] shift_out;

  generate
    if (num_ch == 6) begin
      // YM2612 / YM3438: Two CSR.
      wire [43:0] shift_middle;

      jt12_csr u_csr0 (
          .rst                    (rst),
          .clk                    (clk),
          .clk_en                 (clk_en),
          .din                    (din),
          .shift_in               (shift_out),
          .shift_out              (shift_middle),
          .up_tl                  (up_tl),
          .up_dt1                 (up_dt1),
          .up_ks_ar               (up_ks_ar),
          .up_amen_dr             (up_amen_dr),
          .up_sr                  (up_sr),
          .up_sl_rr               (up_sl_rr),
          .up_ssgeg               (up_ssgeg),
          .update_op_I            (update_op_I),
          .update_op_II           (update_op_II),
          .update_op_IV           (update_op_IV),
          .auto_ss_rd             (auto_ss_rd),
          .auto_ss_wr             (auto_ss_wr),
          .auto_ss_data_in        (auto_ss_data_in),
          .auto_ss_device_idx     (auto_ss_device_idx),
          .auto_ss_state_idx      (auto_ss_state_idx),
          .auto_ss_base_device_idx(auto_ss_base_device_idx + 8),
          .auto_ss_data_out       (auto_ss_u_csr0_data_out),
          .auto_ss_ack            (auto_ss_u_csr0_ack)

      );

      wire up_midop_I = {~cur[4], cur[3:0]} == req_opch_I;
      wire up_midop_II = {~cur[4], cur[3:0]} == req_opch_II;
      wire up_midop_IV = {~cur[4], cur[3:0]} == req_opch_IV;

      jt12_csr u_csr1 (
          .rst                    (rst),
          .clk                    (clk),
          .clk_en                 (clk_en),
          .din                    (din),
          .shift_in               (shift_middle),
          .shift_out              (shift_out),
          .up_tl                  (up_tl),
          .up_dt1                 (up_dt1),
          .up_ks_ar               (up_ks_ar),
          .up_amen_dr             (up_amen_dr),
          .up_sr                  (up_sr),
          .up_sl_rr               (up_sl_rr),
          .up_ssgeg               (up_ssgeg),
          // update in the middle:
          .update_op_I            (up_midop_I),
          .update_op_II           (up_midop_II),
          .update_op_IV           (up_midop_IV),
          .auto_ss_rd             (auto_ss_rd),
          .auto_ss_wr             (auto_ss_wr),
          .auto_ss_data_in        (auto_ss_data_in),
          .auto_ss_device_idx     (auto_ss_device_idx),
          .auto_ss_state_idx      (auto_ss_state_idx),
          .auto_ss_base_device_idx(auto_ss_base_device_idx + 10),
          .auto_ss_data_out       (auto_ss_u_csr1_data_out),
          .auto_ss_ack            (auto_ss_u_csr1_ack)

      );
    end else begin  // YM2203 only has one CSR
      jt12_csr u_csr0 (
          .rst                    (rst),
          .clk                    (clk),
          .clk_en                 (clk_en),
          .din                    (din),
          .shift_in               (shift_out),
          .shift_out              (shift_out),
          .up_tl                  (up_tl),
          .up_dt1                 (up_dt1),
          .up_ks_ar               (up_ks_ar),
          .up_amen_dr             (up_amen_dr),
          .up_sr                  (up_sr),
          .up_sl_rr               (up_sl_rr),
          .up_ssgeg               (up_ssgeg),
          .update_op_I            (update_op_I),
          .update_op_II           (update_op_II),
          .update_op_IV           (update_op_IV),
          .auto_ss_rd             (auto_ss_rd),
          .auto_ss_wr             (auto_ss_wr),
          .auto_ss_data_in        (auto_ss_data_in),
          .auto_ss_device_idx     (auto_ss_device_idx),
          .auto_ss_state_idx      (auto_ss_state_idx),
          .auto_ss_base_device_idx(auto_ss_base_device_idx + 12),
          .auto_ss_data_out       (auto_ss_u_csr0_data_out),
          .auto_ss_ack            (auto_ss_u_csr0_ack)

      );
    end  // else
  endgenerate

  assign { tl_IV,   dt1_I,    mul_II,    ks_II, 
         ar_I,    amsen_IV, d1r_I,     d2r_I, 
         sl_I,    rr_I,     ssg_en_I,  ssg_eg_I } = shift_out;


  // memory for CH registers
  jt12_reg_ch #(
      .NUM_CH(num_ch)
  ) u_regch (
      .rst(rst),
      .clk(clk),
      .cen(clk_en),
      .din(ch_din),

      .up_ch     (ch_sel),
      .latch_fnum(latch_fnum),
      .up_fnumlo (up_fnumlo),
      .up_alg    (up_alg),
      .up_pms    (up_pms),

      .ch                     (next_ch),                      // next active channel
      .block                  (block_I_raw),
      .fnum                   (fnum_I_raw),
      .fb                     (fb_I),
      .alg                    (alg_I),
      .rl                     (rl),
      .ams_IV                 (ams_IV),
      .pms                    (pms_I),
      .auto_ss_rd             (auto_ss_rd),
      .auto_ss_wr             (auto_ss_wr),
      .auto_ss_data_in        (auto_ss_data_in),
      .auto_ss_device_idx     (auto_ss_device_idx),
      .auto_ss_state_idx      (auto_ss_state_idx),
      .auto_ss_base_device_idx(auto_ss_base_device_idx + 7),
      .auto_ss_data_out       (auto_ss_u_regch_data_out),
      .auto_ss_ack            (auto_ss_u_regch_ack)

  );


endmodule


///////////////////////////////////////////
// MODULE jt12_mmr
module jt12_mmr (
    input rst,
    input clk,
    input cen  /* synthesis direct_enable */,
    output clk_en,
    output clk_en_2,
    output clk_en_ssg,
    output clk_en_666,
    output clk_en_111,
    output clk_en_55,
    input [7:0] din,
    input write,
    input [1:0] addr,
    output reg busy,
    output ch6op,
    output [2:0] cur_ch,
    output [1:0] cur_op,
    // LFO
    output reg [2:0] lfo_freq,
    output reg lfo_en,
    // Timers
    output reg [9:0] value_A,
    output reg [7:0] value_B,
    output reg load_A,
    output reg load_B,
    output reg enable_irq_A,
    output reg enable_irq_B,
    output reg clr_flag_A,
    output reg clr_flag_B,
    output reg fast_timers,
    input flag_A,
    input overflow_A,
    output reg [1:0] div_setting,
    // PCM
    output reg [8:0] pcm,
    output reg pcm_en,
    output reg pcm_wr,  // high for one clock cycle when PCM is written
    // ADPCM-A
    output reg [7:0] aon_a,  // ON
    output reg [5:0] atl_a,  // TL
    output reg [15:0] addr_a,  // address latch
    output reg [7:0] lracl,  // L/R ADPCM Channel Level
    output reg up_start,  // write enable start address latch
    output reg up_end,  // write enable end address latch
    output reg [2:0] up_addr,  // write enable end address latch
    output reg [2:0] up_lracl,
    output reg up_aon,  // There was a write AON register
    // ADPCM-B
    output reg acmd_on_b,  // Control - Process start, Key On
    output reg acmd_rep_b,  // Control - Repeat
    output reg acmd_rst_b,  // Control - Reset
    output reg acmd_up_b,  // Control - New cmd received
    output reg [1:0] alr_b,  // Left / Right
    output reg [15:0] astart_b,  // Start address
    output reg [15:0] aend_b,  // End   address
    output reg [15:0] adeltan_b,  // Delta-N
    output reg [7:0] aeg_b,  // Envelope Generator Control
    output reg [6:0] flag_ctl,
    output reg [6:0] flag_mask,
    // Operator
    output xuse_prevprev1,
    output xuse_internal,
    output yuse_internal,
    output xuse_prev2,
    output yuse_prev1,
    output yuse_prev2,
    // PG
    output [10:0] fnum_I,
    output [2:0] block_I,
    output reg pg_stop,
    // REG
    output [1:0] rl,
    output [2:0] fb_II,
    output [2:0] alg_I,
    output [2:0] pms_I,
    output [1:0] ams_IV,
    output amsen_IV,
    output [2:0] dt1_I,
    output [3:0] mul_II,
    output [6:0] tl_IV,
    output reg eg_stop,

    output [4:0] ar_I,
    output [4:0] d1r_I,
    output [4:0] d2r_I,
    output [3:0] rr_I,
    output [3:0] sl_I,
    output [1:0] ks_II,
    // SSG operation
    output       ssg_en_I,
    output [2:0] ssg_eg_I,

    output keyon_I,

    // Operator
    output zero,
    output s1_enters,
    output s2_enters,
    output s3_enters,
    output s4_enters,

    // PSG interace
    output       [ 3:0] psg_addr,
    output       [ 7:0] psg_data,
    output reg          psg_wr_n,
    input        [ 7:0] debug_bus,
    input               auto_ss_rd,
    input               auto_ss_wr,
    input        [31:0] auto_ss_data_in,
    input        [ 7:0] auto_ss_device_idx,
    input        [15:0] auto_ss_state_idx,
    input        [ 7:0] auto_ss_base_device_idx,
    output logic [31:0] auto_ss_data_out,
    output logic        auto_ss_ack

);
  assign auto_ss_ack = auto_ss_local_ack | auto_ss_u_div_ack | auto_ss_u_reg_ack;

  assign auto_ss_data_out = auto_ss_local_data_out | auto_ss_u_div_data_out | auto_ss_u_reg_data_out;

  logic        auto_ss_local_ack;

  logic [31:0] auto_ss_local_data_out;

  wire         auto_ss_u_reg_ack;

  wire  [31:0] auto_ss_u_reg_data_out;

  wire         auto_ss_u_div_ack;

  wire  [31:0] auto_ss_u_div_data_out;

  wire         device_match = (auto_ss_device_idx == auto_ss_base_device_idx);

  genvar auto_ss_idx;


  parameter use_ssg = 0, num_ch = 6, use_pcm = 1, use_adpcm = 0, mask_div = 1;

  jt12_div #(
      .use_ssg(use_ssg)
  ) u_div (
      .rst                    (rst),
      .clk                    (clk),
      .cen                    (cen),
      .div_setting            (div_setting),
      .clk_en                 (clk_en),
      .clk_en_2               (clk_en_2),
      .clk_en_ssg             (clk_en_ssg),
      .clk_en_666             (clk_en_666),
      .clk_en_111             (clk_en_111),
      .clk_en_55              (clk_en_55),
      .auto_ss_rd             (auto_ss_rd),
      .auto_ss_wr             (auto_ss_wr),
      .auto_ss_data_in        (auto_ss_data_in),
      .auto_ss_device_idx     (auto_ss_device_idx),
      .auto_ss_state_idx      (auto_ss_state_idx),
      .auto_ss_base_device_idx(auto_ss_base_device_idx + 1),
      .auto_ss_data_out       (auto_ss_u_div_data_out),
      .auto_ss_ack            (auto_ss_u_div_ack)

  );

  reg [7:0] selected_register;

  /*
reg     irq_zero_en, irq_brdy_en, irq_eos_en,
        irq_tb_en, irq_ta_en;
        */
  reg [6:0] up_opreg;  // hot-one encoding. tells which operator register gets updated next
  reg [2:0] up_chreg;  // hot-one encoding. tells which channel register gets updated next
  reg       up_keyon;

  localparam  REG_TESTYM  =   8'h21,
            REG_LFO     =   8'h22,
            REG_CLKA1   =   8'h24,
            REG_CLKA2   =   8'h25,
            REG_CLKB    =   8'h26,
            REG_TIMER   =   8'h27,
            REG_KON     =   8'h28,
            REG_IRQMASK =   8'h29,
            REG_PCM     =   8'h2A,
            REG_PCM_EN  =   8'h2B,
            REG_DACTEST =   8'h2C,
            REG_CLK_N6  =   8'h2D,
            REG_CLK_N3  =   8'h2E,
            REG_CLK_N2  =   8'h2F,
  // ADPCM (YM2610)
  REG_ADPCMA_ON = 8'h00, REG_ADPCMA_TL = 8'h01, REG_ADPCMA_TEST = 8'h02;

  reg csm, effect;

  reg [2:0] block_ch3op2, block_ch3op3, block_ch3op1;
  reg [10:0] fnum_ch3op2, fnum_ch3op3, fnum_ch3op1;
  reg [5:0] latch_fnum;


  reg [2:0] up_ch;
  reg [1:0] up_op;

  reg [7:0] op_din, ch_din;

  generate
    if (use_ssg) begin
      assign psg_addr = selected_register[3:0];
      assign psg_data = ch_din;
    end else begin
      assign psg_addr = 4'd0;
      assign psg_data = 8'd0;
    end
  endgenerate

  reg        part;



  wire [2:0] ch_sel = {part, selected_register[1:0]};

  // this runs at clk speed, no clock gating here
  // if I try to make this an async rst it fails to map it
  // as flip flops but uses latches instead. So I keep it as sync. reset
  always @(posedge clk) begin
    begin : memory_mapped_registers
      if (rst) begin
        selected_register <= 0;
        div_setting <= 2'b10;  // FM=1/6, SSG=1/4
        up_ch <= 0;
        up_op <= 0;
        up_keyon <= 0;
        up_opreg <= 0;
        up_chreg <= 0;
        // IRQ Mask
        /*{ irq_zero_en, irq_brdy_en, irq_eos_en,
            irq_tb_en, irq_ta_en } = 5'h1f; */
        // timers
        {value_A, value_B} <= 0;
        {clr_flag_B, clr_flag_A, enable_irq_B, enable_irq_A, load_B, load_A} <= 0;
        fast_timers <= 0;
        // LFO
        lfo_freq <= 0;
        lfo_en <= 0;
        csm <= 0;
        effect <= 0;
        // PCM
        pcm <= 0;
        pcm_en <= 0;
        pcm_wr <= 0;
        // ADPCM-A
        aon_a <= 0;
        atl_a <= 0;
        up_start <= 0;
        up_end <= 0;
        up_addr <= 7;
        up_lracl <= 7;
        up_aon <= 0;
        lracl <= 0;
        addr_a <= 0;
        // ADPCM-B
        acmd_on_b <= 0;
        acmd_rep_b <= 0;
        acmd_rst_b <= 0;
        alr_b <= 0;
        flag_ctl <= 0;
        astart_b <= 0;
        aend_b <= 0;
        adeltan_b <= 0;
        flag_mask <= 0;
        aeg_b <= 8'hff;
        // Original test features
        eg_stop <= 0;
        pg_stop <= 0;
        psg_wr_n <= 1;
        // 
        {block_ch3op1, fnum_ch3op1} <= {3'd0, 11'd0};
        {block_ch3op3, fnum_ch3op3} <= {3'd0, 11'd0};
        {block_ch3op2, fnum_ch3op2} <= {3'd0, 11'd0};
        latch_fnum <= 0;
        op_din <= 0;
        part <= 0;
      end else begin
        up_chreg <= 0;
        // WRITE IN REGISTERS
        if (write) begin
          if (!addr[0]) begin
            selected_register <= din;
            part              <= addr[1];
            if (!mask_div)
              case (din)
                // clock divider: should work only for ym2203
                // and ym2608.
                // clock divider works just by selecting the register
                REG_CLK_N6: div_setting[1] <= 1'b1; // 2D
                REG_CLK_N3: div_setting[0] <= 1'b1; // 2E
                REG_CLK_N2: div_setting    <= 2'b0; // 2F
                default:;
              endcase
          end else begin
            // Global registers
            ch_din <= din;
            if (selected_register == REG_KON && !part) begin
              up_keyon <= 1;
              op_din   <= din;
            end else begin
              up_keyon <= 0;
            end
            // General control (<0x20 registers and A0==0)
            if (!part) begin
              casez (selected_register)
                //REG_TEST: lfo_rst <= 1'b1; // regardless of din
                8'h0?:     psg_wr_n <= 1'b0;
                REG_TESTYM: begin
                  eg_stop     <= din[5];
                  pg_stop     <= din[3];
                  fast_timers <= din[2];
                end
                REG_CLKA1: value_A[9:2] <= din;
                REG_CLKA2: value_A[1:0] <= din[1:0];
                REG_CLKB:  value_B <= din;
                REG_TIMER: begin
                  effect <= |din[7:6];
                  csm <= din[7:6] == 2'b10;
                  {clr_flag_B, clr_flag_A, enable_irq_B, enable_irq_A, load_B, load_A} <= din[5:0];
                end

                REG_LFO: {lfo_en, lfo_freq} <= din[3:0];

                default: ;
              endcase
            end

            // CH3 special registers
            casez (selected_register)
              8'hA9: {block_ch3op1, fnum_ch3op1} <= {latch_fnum, din};
              8'hA8: {block_ch3op3, fnum_ch3op3} <= {latch_fnum, din};
              8'hAA: {block_ch3op2, fnum_ch3op2} <= {latch_fnum, din};
              // According to http://www.mjsstuf.x10host.com/pages/vgmPlay/vgmPlay.htm
              // There is a single fnum latch for all channels
              8'hA4, 8'hA5, 8'hA6, 8'hAD, 8'hAC, 8'hAE: latch_fnum <= din[5:0];
              default: ;  // avoid incomplete-case warning
            endcase

            // YM2612 PCM support
            if (use_pcm == 1) begin
              casez (selected_register)
                REG_DACTEST: pcm[0] <= din[3];
                REG_PCM: pcm <= {~din[7], din[6:0], 1'b1};
                REG_PCM_EN: pcm_en <= din[7];
                default: ;
              endcase
              pcm_wr <= selected_register == REG_PCM;
            end
            if (use_adpcm == 1) begin
              // YM2610 ADPCM-A support, A1=1, regs 0-2D
              if (part && selected_register[7:6] == 2'b0) begin
                casez (selected_register[5:0])
                  6'h0: begin
                    aon_a  <= din;
                    up_aon <= 1'b1;
                  end
                  6'h1: atl_a <= din[5:0];
                  // LRACL
                  6'h8, 6'h9, 6'hA, 6'hB, 6'hC, 6'hD: begin
                    lracl    <= din;
                    up_lracl <= selected_register[2:0];
                  end
                  6'b01_????, 6'b10_????: begin
                    if (!selected_register[3]) addr_a[7:0] <= din;
                    if (selected_register[3]) addr_a[15:8] <= din;
                    case (selected_register[5:4])
                      2'b01, 2'b10: begin
                        {up_end, up_start} <= selected_register[5:4];
                        up_addr            <= selected_register[2:0];
                      end
                      default: begin
                        up_start <= 1'b0;
                        up_end   <= 1'b0;
                      end
                    endcase
                  end
                  default: ;
                endcase
              end
              if (!part && selected_register[7:4] == 4'h1) begin
                // YM2610 ADPCM-B support, A1=0, regs 1x
                case (selected_register[3:0])
                  4'd0:
                  {acmd_up_b, acmd_on_b, acmd_rep_b, acmd_rst_b} <= {1'd1, din[7], din[4], din[0]};
                  4'd1: alr_b <= din[7:6];
                  4'd2: astart_b[7:0] <= din;
                  4'd3: astart_b[15:8] <= din;
                  4'd4: aend_b[7:0] <= din;
                  4'd5: aend_b[15:8] <= din;
                  4'h9: adeltan_b[7:0] <= din;
                  4'ha: adeltan_b[15:8] <= din;
                  4'hb: aeg_b <= din;
                  4'hc: begin
                    flag_mask <= ~{din[7], din[5:0]};
                    flag_ctl  <= {din[7], din[5:0]};  // this lasts a single clock cycle
                  end
                  default: ;
                endcase
              end
            end
            if (selected_register[1:0] == 2'b11) {up_chreg, up_opreg} <= {3'h0, 7'h0};
            else begin
              casez (selected_register)
                // channel registers
                8'hA0, 8'hA1, 8'hA2:    { up_chreg, up_opreg } <= { 3'h1, 7'd0 }; // up_fnumlo
                // FB + Algorithm
                8'hB0, 8'hB1, 8'hB2: { up_chreg, up_opreg } <= { 3'h2, 7'd0 }; // up_alg
                8'hB4, 8'hB5, 8'hB6: { up_chreg, up_opreg } <= { 3'h4, 7'd0 }; // up_pms
                // operator registers
                8'h3?: { up_chreg, up_opreg } <= { 3'h0, 7'h01 }; // up_dt1
                8'h4?: { up_chreg, up_opreg } <= { 3'h0, 7'h02 }; // up_tl
                8'h5?: { up_chreg, up_opreg } <= { 3'h0, 7'h04 }; // up_ks_ar
                8'h6?: { up_chreg, up_opreg } <= { 3'h0, 7'h08 }; // up_amen_dr
                8'h7?: { up_chreg, up_opreg } <= { 3'h0, 7'h10 }; // up_sr
                8'h8?: { up_chreg, up_opreg } <= { 3'h0, 7'h20 }; // up_sl
                8'h9?: { up_chreg, up_opreg } <= { 3'h0, 7'h40 }; // up_ssgeg
                default: { up_chreg, up_opreg } <= { 3'h0, 7'h0 };
              endcase  // selected_register
              if (selected_register[7:4] >= 3 && selected_register[7:4] <= 9) begin
                op_din <= din;
                up_ch  <= {part, selected_register[1:0]};
                up_op  <= selected_register[3:2];  // 0=S1,1=S3,2=S2,3=S4
              end
            end
          end
        end else if (clk_en) begin  /* clear once-only bits */
          // lfo_rst <= 1'b0;
          {clr_flag_B, clr_flag_A} <= 2'd0;
          psg_wr_n                 <= 1'b1;
          pcm_wr                   <= 1'b0;
          flag_ctl                 <= 'd0;
          up_aon                   <= 1'b0;
          acmd_up_b                <= 1'b0;
        end
      end
    end
    if (auto_ss_wr && device_match) begin
      case (auto_ss_state_idx)
        0: begin
          addr_a    <= auto_ss_data_in[15:0];
          adeltan_b <= auto_ss_data_in[31:16];
        end
        1: begin
          aend_b   <= auto_ss_data_in[15:0];
          astart_b <= auto_ss_data_in[31:16];
        end
        2: begin
          value_A <= auto_ss_data_in[9:0];
          pcm     <= auto_ss_data_in[18:10];
          aeg_b   <= auto_ss_data_in[26:19];
        end
        3: begin
          aon_a  <= auto_ss_data_in[7:0];
          ch_din <= auto_ss_data_in[15:8];
          lracl  <= auto_ss_data_in[23:16];
          op_din <= auto_ss_data_in[31:24];
        end
        4: begin
          selected_register <= auto_ss_data_in[7:0];
          value_B           <= auto_ss_data_in[15:8];
          flag_ctl          <= auto_ss_data_in[22:16];
          flag_mask         <= auto_ss_data_in[29:23];
        end
        5: begin
          up_opreg     <= auto_ss_data_in[6:0];
          atl_a        <= auto_ss_data_in[12:7];
          latch_fnum   <= auto_ss_data_in[18:13];
          block_ch3op1 <= auto_ss_data_in[26:24];
          block_ch3op2 <= auto_ss_data_in[29:27];
        end
        6: begin
          block_ch3op3 <= auto_ss_data_in[2:0];
          lfo_freq     <= auto_ss_data_in[5:3];
          up_addr      <= auto_ss_data_in[8:6];
          up_ch        <= auto_ss_data_in[11:9];
          up_chreg     <= auto_ss_data_in[14:12];
          up_lracl     <= auto_ss_data_in[17:15];
          alr_b        <= auto_ss_data_in[19:18];
          div_setting  <= auto_ss_data_in[21:20];
          up_op        <= auto_ss_data_in[23:22];
          acmd_on_b    <= auto_ss_data_in[24];
          acmd_rep_b   <= auto_ss_data_in[25];
          acmd_rst_b   <= auto_ss_data_in[26];
          acmd_up_b    <= auto_ss_data_in[27];
          clr_flag_B   <= auto_ss_data_in[28];
          csm          <= auto_ss_data_in[29];
          effect       <= auto_ss_data_in[30];
          eg_stop      <= auto_ss_data_in[31];
        end
        7: begin
          fast_timers <= auto_ss_data_in[0];
          lfo_en      <= auto_ss_data_in[1];
          part        <= auto_ss_data_in[2];
          pcm_en      <= auto_ss_data_in[3];
          pcm_wr      <= auto_ss_data_in[4];
          pg_stop     <= auto_ss_data_in[5];
          psg_wr_n    <= auto_ss_data_in[6];
          up_aon      <= auto_ss_data_in[7];
          up_end      <= auto_ss_data_in[8];
          up_keyon    <= auto_ss_data_in[9];
          up_start    <= auto_ss_data_in[10];
        end
        default: begin
        end
      endcase
    end
  end



  reg  [4:0] busy_cnt;  // busy lasts for 32 synthesizer clock cycles
  wire [5:0] nx_busy = {1'd0, busy_cnt} + {5'd0, busy};

  always @(posedge clk, posedge rst) begin
    if (rst) begin
      busy     <= 0;
      busy_cnt <= 0;
    end else if (auto_ss_wr && device_match) begin
      case (auto_ss_state_idx)
        5: begin
          busy_cnt <= auto_ss_data_in[23:19];
        end
        7: begin
          busy <= auto_ss_data_in[11];
        end
        default: begin
        end
      endcase
    end else begin
      if (write & addr[0]) begin
        busy     <= 1;
        busy_cnt <= 0;
      end else if (clk_en) begin
        busy     <= ~nx_busy[5] & busy;
        busy_cnt <= nx_busy[4:0];
      end
    end
  end
  always_comb begin
    auto_ss_local_data_out = 32'h0;
    auto_ss_local_ack      = 1'b0;
    if (auto_ss_rd && device_match) begin
      case (auto_ss_state_idx)
        0: begin
          auto_ss_local_data_out[31:0] = {adeltan_b, addr_a};
          auto_ss_local_ack            = 1'b1;
        end
        1: begin
          auto_ss_local_data_out[31:0] = {astart_b, aend_b};
          auto_ss_local_ack            = 1'b1;
        end
        2: begin
          auto_ss_local_data_out[26:0] = {aeg_b, pcm, value_A};
          auto_ss_local_ack            = 1'b1;
        end
        3: begin
          auto_ss_local_data_out[31:0] = {op_din, lracl, ch_din, aon_a};
          auto_ss_local_ack            = 1'b1;
        end
        4: begin
          auto_ss_local_data_out[29:0] = {flag_mask, flag_ctl, value_B, selected_register};
          auto_ss_local_ack            = 1'b1;
        end
        5: begin
          auto_ss_local_data_out[29:0] = {
            block_ch3op2, block_ch3op1, busy_cnt, latch_fnum, atl_a, up_opreg
          };
          auto_ss_local_ack = 1'b1;
        end
        6: begin
          auto_ss_local_data_out[31:0] = {
            eg_stop,
            effect,
            csm,
            clr_flag_B,
            acmd_up_b,
            acmd_rst_b,
            acmd_rep_b,
            acmd_on_b,
            up_op,
            div_setting,
            alr_b,
            up_lracl,
            up_chreg,
            up_ch,
            up_addr,
            lfo_freq,
            block_ch3op3
          };
          auto_ss_local_ack = 1'b1;
        end
        7: begin
          auto_ss_local_data_out[11:0] = {
            busy,
            up_start,
            up_keyon,
            up_end,
            up_aon,
            psg_wr_n,
            pg_stop,
            pcm_wr,
            pcm_en,
            part,
            lfo_en,
            fast_timers
          };
          auto_ss_local_ack = 1'b1;
        end
        default: begin
        end
      endcase
    end
  end



  jt12_reg #(
      .num_ch(num_ch)
  ) u_reg (
      .rst   (rst),
      .clk   (clk),    // P1
      .clk_en(clk_en),

      // channel udpates
      .ch_sel   (ch_sel),
      .ch_din   (ch_din),
      .up_fnumlo(up_chreg[0]),
      .up_alg   (up_chreg[1]),
      .up_pms   (up_chreg[2]),

      // operator updates
      .din       (op_din),
      .up_keyon  (up_keyon),
      .up_dt1    (up_opreg[0]),
      .up_tl     (up_opreg[1]),
      .up_ks_ar  (up_opreg[2]),
      .up_amen_dr(up_opreg[3]),
      .up_sr     (up_opreg[4]),
      .up_sl_rr  (up_opreg[5]),
      .up_ssgeg  (up_opreg[6]),

      .op(up_op),  // operator to update
      .ch(up_ch),  // channel to update

      .csm       (csm),
      .flag_A    (flag_A),
      .overflow_A(overflow_A),

      .ch6op         (ch6op),
      .cur_ch        (cur_ch),
      .cur_op        (cur_op),
      // CH3 Effect-mode operation
      .effect        (effect),          // allows independent freq. for CH 3
      .fnum_ch3op2   (fnum_ch3op2),
      .fnum_ch3op3   (fnum_ch3op3),
      .fnum_ch3op1   (fnum_ch3op1),
      .block_ch3op2  (block_ch3op2),
      .block_ch3op3  (block_ch3op3),
      .block_ch3op1  (block_ch3op1),
      .latch_fnum    (latch_fnum),
      // Operator
      .xuse_prevprev1(xuse_prevprev1),
      .xuse_internal (xuse_internal),
      .yuse_internal (yuse_internal),
      .xuse_prev2    (xuse_prev2),
      .yuse_prev1    (yuse_prev1),
      .yuse_prev2    (yuse_prev2),
      // PG
      .fnum_I        (fnum_I),
      .block_I       (block_I),
      .mul_II        (mul_II),
      .dt1_I         (dt1_I),

      // EG
      .ar_I    (ar_I),      // attack  rate
      .d1r_I   (d1r_I),     // decay   rate
      .d2r_I   (d2r_I),     // sustain rate
      .rr_I    (rr_I),      // release rate
      .sl_I    (sl_I),      // sustain level
      .ks_II   (ks_II),     // key scale
      // SSG operation
      .ssg_en_I(ssg_en_I),
      .ssg_eg_I(ssg_eg_I),
      // envelope number
      .tl_IV   (tl_IV),
      .pms_I   (pms_I),
      .ams_IV  (ams_IV),
      .amsen_IV(amsen_IV),
      // channel configuration
      .rl      (rl),
      .fb_II   (fb_II),
      .alg_I   (alg_I),
      .keyon_I (keyon_I),

      .zero                   (zero),
      .s1_enters              (s1_enters),
      .s2_enters              (s2_enters),
      .s3_enters              (s3_enters),
      .s4_enters              (s4_enters),
      .auto_ss_rd             (auto_ss_rd),
      .auto_ss_wr             (auto_ss_wr),
      .auto_ss_data_in        (auto_ss_data_in),
      .auto_ss_device_idx     (auto_ss_device_idx),
      .auto_ss_state_idx      (auto_ss_state_idx),
      .auto_ss_base_device_idx(auto_ss_base_device_idx + 2),
      .auto_ss_data_out       (auto_ss_u_reg_data_out),
      .auto_ss_ack            (auto_ss_u_reg_ack)

  );

endmodule


///////////////////////////////////////////
// MODULE jt12_timer
module jt12_timer #(
    parameter CW      = 8,  // counter bit width. This is the counter that can be loaded
              FW      = 4,  // number of bits for the free-running counter
              FREE_EN = 0   // enables a 4-bit free enable count
) (
    input                 rst,
    input                 clk,
    input                 cen,
    input                 zero,
    input        [CW-1:0] start_value,
    input                 load,
    input                 clr_flag,
    output reg            flag,
    output reg            overflow,
    input                 auto_ss_rd,
    input                 auto_ss_wr,
    input        [  31:0] auto_ss_data_in,
    input        [   7:0] auto_ss_device_idx,
    input        [  15:0] auto_ss_state_idx,
    input        [   7:0] auto_ss_base_device_idx,
    output logic [  31:0] auto_ss_data_out,
    output logic          auto_ss_ack

);
  wire device_match = (auto_ss_device_idx == auto_ss_base_device_idx);

  genvar auto_ss_idx;

  /* verilator lint_off WIDTH */
  reg load_l;
  reg [CW-1:0] cnt, next;
  reg [FW-1:0] free_cnt, free_next;
  reg free_ov;

  always @(posedge clk, posedge rst)
    if (rst) flag <= 1'b0;
    else if (auto_ss_wr && device_match) begin
      case (auto_ss_state_idx)
        0: begin
          flag <= auto_ss_data_in[0];
        end
        default: begin
        end
      endcase
    end else  /*if(cen)*/ begin
      if (clr_flag) flag <= 1'b0;
      else if (cen && zero && load && overflow) flag <= 1'b1;
    end

  always @(*) begin
    {free_ov, free_next} = {1'b0, free_cnt} + 1'b1;
    {overflow, next}     = {1'b0, cnt} + (FREE_EN ? free_ov : 1'b1);
  end

  always @(posedge clk) begin
    begin
      load_l <= load;
      if (!load_l && load) begin
        cnt <= start_value;
      end else if (cen && zero && load) cnt <= overflow ? start_value : next;
    end
    if (auto_ss_wr && device_match) begin
      case (auto_ss_state_idx)
        0: begin
          load_l <= auto_ss_data_in[1];
        end
        default: begin
        end
      endcase
    end
  end



  // Free running counter
  always @(posedge clk) begin
    begin
      if (rst) begin
        free_cnt <= 0;
      end else if (cen && zero) begin
        free_cnt <= free_next;
      end
    end
    if (auto_ss_wr && device_match) begin
    end
  end


  always_comb begin
    auto_ss_data_out = 32'h0;
    auto_ss_ack      = 1'b0;
    if (auto_ss_rd && device_match) begin
      case (auto_ss_state_idx)
        0: begin
          auto_ss_data_out[1:0] = {load_l, flag};
          auto_ss_ack           = 1'b1;
        end
        default: begin
        end
      endcase
    end
  end


  /* verilator lint_on WIDTH */
endmodule


///////////////////////////////////////////
// MODULE jt12_timers
module jt12_timers (
    input               clk,
    input               rst,
    input               clk_en  /* synthesis direct_enable */,
    input               zero,
    input        [ 9:0] value_A,
    input        [ 7:0] value_B,
    input               load_A,
    input               load_B,
    input               clr_flag_A,
    input               clr_flag_B,
    input               enable_irq_A,
    input               enable_irq_B,
    output              flag_A,
    output              flag_B,
    output              overflow_A,
    output              irq_n,
    input               auto_ss_rd,
    input               auto_ss_wr,
    input        [31:0] auto_ss_data_in,
    input        [ 7:0] auto_ss_device_idx,
    input        [15:0] auto_ss_state_idx,
    input        [ 7:0] auto_ss_base_device_idx,
    output logic [31:0] auto_ss_data_out,
    output logic        auto_ss_ack

);
  assign auto_ss_ack      = auto_ss_timer_A_ack | auto_ss_timer_B_ack;

  assign auto_ss_data_out = auto_ss_timer_A_data_out | auto_ss_timer_B_data_out;

  wire        auto_ss_timer_B_ack;

  wire [31:0] auto_ss_timer_B_data_out;

  wire        auto_ss_timer_A_ack;

  wire [31:0] auto_ss_timer_A_data_out;

  wire        device_match = (auto_ss_device_idx == auto_ss_base_device_idx);

  genvar auto_ss_idx;


  parameter num_ch = 6;

  assign irq_n = ~((flag_A & enable_irq_A) | (flag_B & enable_irq_B));

  /*
reg zero2;

always @(posedge clk, posedge rst) begin
    if( rst )
        zero2 <= 0;
    else if(clk_en) begin
        if( zero ) zero2 <= ~zero;
    end
end

wire zero       = num_ch == 6 ? zero : (zero2&zero);
*/
  jt12_timer #(
      .CW(10)
  ) timer_A (
      .clk                    (clk),
      .rst                    (rst),
      .cen                    (clk_en),
      .zero                   (zero),
      .start_value            (value_A),
      .load                   (load_A),
      .clr_flag               (clr_flag_A),
      .flag                   (flag_A),
      .overflow               (overflow_A),
      .auto_ss_rd             (auto_ss_rd),
      .auto_ss_wr             (auto_ss_wr),
      .auto_ss_data_in        (auto_ss_data_in),
      .auto_ss_device_idx     (auto_ss_device_idx),
      .auto_ss_state_idx      (auto_ss_state_idx),
      .auto_ss_base_device_idx(auto_ss_base_device_idx + 1),
      .auto_ss_data_out       (auto_ss_timer_A_data_out),
      .auto_ss_ack            (auto_ss_timer_A_ack)

  );

  jt12_timer #(
      .CW     (8),
      .FREE_EN(1)
  ) timer_B (
      .clk                    (clk),
      .rst                    (rst),
      .cen                    (clk_en),
      .zero                   (zero),
      .start_value            (value_B),
      .load                   (load_B),
      .clr_flag               (clr_flag_B),
      .flag                   (flag_B),
      .overflow               (),
      .auto_ss_rd             (auto_ss_rd),
      .auto_ss_wr             (auto_ss_wr),
      .auto_ss_data_in        (auto_ss_data_in),
      .auto_ss_device_idx     (auto_ss_device_idx),
      .auto_ss_state_idx      (auto_ss_state_idx),
      .auto_ss_base_device_idx(auto_ss_base_device_idx + 2),
      .auto_ss_data_out       (auto_ss_timer_B_data_out),
      .auto_ss_ack            (auto_ss_timer_B_ack)

  );

endmodule


///////////////////////////////////////////
// MODULE jt12_pm
module jt12_pm (
    input             [ 4:0] lfo_mod,
    input             [10:0] fnum,
    input             [ 2:0] pms,
    output reg signed [ 8:0] pm_offset
);


  reg  [7:0] pm_unsigned;
  reg  [7:0] pm_base;
  reg  [9:0] pm_shifted;

  wire [2:0] index = lfo_mod[3] ? (~lfo_mod[2:0]) : lfo_mod[2:0];

  reg  [2:0] lfo_sh1_lut                                         [0:63];
  reg  [2:0] lfo_sh2_lut                                         [0:63];
  reg [2:0] lfo_sh1, lfo_sh2;

  initial begin
    lfo_sh1_lut[6'h00] = 3'd7;
    lfo_sh1_lut[6'h01] = 3'd7;
    lfo_sh1_lut[6'h02] = 3'd7;
    lfo_sh1_lut[6'h03] = 3'd7;
    lfo_sh1_lut[6'h04] = 3'd7;
    lfo_sh1_lut[6'h05] = 3'd7;
    lfo_sh1_lut[6'h06] = 3'd7;
    lfo_sh1_lut[6'h07] = 3'd7;
    lfo_sh1_lut[6'h08] = 3'd7;
    lfo_sh1_lut[6'h09] = 3'd7;
    lfo_sh1_lut[6'h0A] = 3'd7;
    lfo_sh1_lut[6'h0B] = 3'd7;
    lfo_sh1_lut[6'h0C] = 3'd7;
    lfo_sh1_lut[6'h0D] = 3'd7;
    lfo_sh1_lut[6'h0E] = 3'd7;
    lfo_sh1_lut[6'h0F] = 3'd7;
    lfo_sh1_lut[6'h10] = 3'd7;
    lfo_sh1_lut[6'h11] = 3'd7;
    lfo_sh1_lut[6'h12] = 3'd7;
    lfo_sh1_lut[6'h13] = 3'd7;
    lfo_sh1_lut[6'h14] = 3'd7;
    lfo_sh1_lut[6'h15] = 3'd7;
    lfo_sh1_lut[6'h16] = 3'd1;
    lfo_sh1_lut[6'h17] = 3'd1;
    lfo_sh1_lut[6'h18] = 3'd7;
    lfo_sh1_lut[6'h19] = 3'd7;
    lfo_sh1_lut[6'h1A] = 3'd7;
    lfo_sh1_lut[6'h1B] = 3'd7;
    lfo_sh1_lut[6'h1C] = 3'd1;
    lfo_sh1_lut[6'h1D] = 3'd1;
    lfo_sh1_lut[6'h1E] = 3'd1;
    lfo_sh1_lut[6'h1F] = 3'd1;
    lfo_sh1_lut[6'h20] = 3'd7;
    lfo_sh1_lut[6'h21] = 3'd7;
    lfo_sh1_lut[6'h22] = 3'd7;
    lfo_sh1_lut[6'h23] = 3'd1;
    lfo_sh1_lut[6'h24] = 3'd1;
    lfo_sh1_lut[6'h25] = 3'd1;
    lfo_sh1_lut[6'h26] = 3'd1;
    lfo_sh1_lut[6'h27] = 3'd0;
    lfo_sh1_lut[6'h28] = 3'd7;
    lfo_sh1_lut[6'h29] = 3'd7;
    lfo_sh1_lut[6'h2A] = 3'd1;
    lfo_sh1_lut[6'h2B] = 3'd1;
    lfo_sh1_lut[6'h2C] = 3'd0;
    lfo_sh1_lut[6'h2D] = 3'd0;
    lfo_sh1_lut[6'h2E] = 3'd0;
    lfo_sh1_lut[6'h2F] = 3'd0;
    lfo_sh1_lut[6'h30] = 3'd7;
    lfo_sh1_lut[6'h31] = 3'd7;
    lfo_sh1_lut[6'h32] = 3'd1;
    lfo_sh1_lut[6'h33] = 3'd1;
    lfo_sh1_lut[6'h34] = 3'd0;
    lfo_sh1_lut[6'h35] = 3'd0;
    lfo_sh1_lut[6'h36] = 3'd0;
    lfo_sh1_lut[6'h37] = 3'd0;
    lfo_sh1_lut[6'h38] = 3'd7;
    lfo_sh1_lut[6'h39] = 3'd7;
    lfo_sh1_lut[6'h3A] = 3'd1;
    lfo_sh1_lut[6'h3B] = 3'd1;
    lfo_sh1_lut[6'h3C] = 3'd0;
    lfo_sh1_lut[6'h3D] = 3'd0;
    lfo_sh1_lut[6'h3E] = 3'd0;
    lfo_sh1_lut[6'h3F] = 3'd0;
    lfo_sh2_lut[6'h00] = 3'd7;
    lfo_sh2_lut[6'h01] = 3'd7;
    lfo_sh2_lut[6'h02] = 3'd7;
    lfo_sh2_lut[6'h03] = 3'd7;
    lfo_sh2_lut[6'h04] = 3'd7;
    lfo_sh2_lut[6'h05] = 3'd7;
    lfo_sh2_lut[6'h06] = 3'd7;
    lfo_sh2_lut[6'h07] = 3'd7;
    lfo_sh2_lut[6'h08] = 3'd7;
    lfo_sh2_lut[6'h09] = 3'd7;
    lfo_sh2_lut[6'h0A] = 3'd7;
    lfo_sh2_lut[6'h0B] = 3'd7;
    lfo_sh2_lut[6'h0C] = 3'd2;
    lfo_sh2_lut[6'h0D] = 3'd2;
    lfo_sh2_lut[6'h0E] = 3'd2;
    lfo_sh2_lut[6'h0F] = 3'd2;
    lfo_sh2_lut[6'h10] = 3'd7;
    lfo_sh2_lut[6'h11] = 3'd7;
    lfo_sh2_lut[6'h12] = 3'd7;
    lfo_sh2_lut[6'h13] = 3'd2;
    lfo_sh2_lut[6'h14] = 3'd2;
    lfo_sh2_lut[6'h15] = 3'd2;
    lfo_sh2_lut[6'h16] = 3'd7;
    lfo_sh2_lut[6'h17] = 3'd7;
    lfo_sh2_lut[6'h18] = 3'd7;
    lfo_sh2_lut[6'h19] = 3'd7;
    lfo_sh2_lut[6'h1A] = 3'd2;
    lfo_sh2_lut[6'h1B] = 3'd2;
    lfo_sh2_lut[6'h1C] = 3'd7;
    lfo_sh2_lut[6'h1D] = 3'd7;
    lfo_sh2_lut[6'h1E] = 3'd2;
    lfo_sh2_lut[6'h1F] = 3'd2;
    lfo_sh2_lut[6'h20] = 3'd7;
    lfo_sh2_lut[6'h21] = 3'd7;
    lfo_sh2_lut[6'h22] = 3'd2;
    lfo_sh2_lut[6'h23] = 3'd7;
    lfo_sh2_lut[6'h24] = 3'd7;
    lfo_sh2_lut[6'h25] = 3'd7;
    lfo_sh2_lut[6'h26] = 3'd2;
    lfo_sh2_lut[6'h27] = 3'd7;
    lfo_sh2_lut[6'h28] = 3'd7;
    lfo_sh2_lut[6'h29] = 3'd7;
    lfo_sh2_lut[6'h2A] = 3'd7;
    lfo_sh2_lut[6'h2B] = 3'd2;
    lfo_sh2_lut[6'h2C] = 3'd7;
    lfo_sh2_lut[6'h2D] = 3'd7;
    lfo_sh2_lut[6'h2E] = 3'd2;
    lfo_sh2_lut[6'h2F] = 3'd1;
    lfo_sh2_lut[6'h30] = 3'd7;
    lfo_sh2_lut[6'h31] = 3'd7;
    lfo_sh2_lut[6'h32] = 3'd7;
    lfo_sh2_lut[6'h33] = 3'd2;
    lfo_sh2_lut[6'h34] = 3'd7;
    lfo_sh2_lut[6'h35] = 3'd7;
    lfo_sh2_lut[6'h36] = 3'd2;
    lfo_sh2_lut[6'h37] = 3'd1;
    lfo_sh2_lut[6'h38] = 3'd7;
    lfo_sh2_lut[6'h39] = 3'd7;
    lfo_sh2_lut[6'h3A] = 3'd7;
    lfo_sh2_lut[6'h3B] = 3'd2;
    lfo_sh2_lut[6'h3C] = 3'd7;
    lfo_sh2_lut[6'h3D] = 3'd7;
    lfo_sh2_lut[6'h3E] = 3'd2;
    lfo_sh2_lut[6'h3F] = 3'd1;
  end

  always @(*) begin
    lfo_sh1 = lfo_sh1_lut[{pms, index}];
    lfo_sh2 = lfo_sh2_lut[{pms, index}];
    pm_base = ({1'b0, fnum[10:4]} >> lfo_sh1) + ({1'b0, fnum[10:4]} >> lfo_sh2);
    case (pms)
      default: pm_shifted = {2'b0, pm_base};
      3'd6:    pm_shifted = {1'b0, pm_base, 1'b0};
      3'd7:    pm_shifted = {pm_base, 2'b0};
    endcase  // pms
    pm_offset = lfo_mod[4] ? (-{1'b0, pm_shifted[9:2]}) : {1'b0, pm_shifted[9:2]};
  end  // always @(*)

endmodule


///////////////////////////////////////////
// MODULE jt12_pg_dt
module jt12_pg_dt (
    input [ 2:0] block,
    input [10:0] fnum,
    input [ 2:0] detune,

    output reg        [4:0] keycode,
    output reg signed [5:0] detune_signed
);

  reg [5:0] detune_kf;
  reg [4:0] pow2;
  reg [5:0] detune_unlimited;
  reg [4:0] detune_limit, detune_limited;


  always @(*) begin
    keycode = {block, fnum[10], fnum[10] ? (|fnum[9:7]) : (&fnum[9:7])};
    case (detune[1:0])
      2'd1: detune_kf = {1'b0, keycode} - 6'd4;
      2'd2: detune_kf = {1'b0, keycode} + 6'd4;
      2'd3: detune_kf = {1'b0, keycode} + 6'd8;
      default: detune_kf = {1'b0, keycode};
    endcase
    case (detune_kf[2:0])
      3'd0: pow2 = 5'd16;
      3'd1: pow2 = 5'd17;
      3'd2: pow2 = 5'd19;
      3'd3: pow2 = 5'd20;
      3'd4: pow2 = 5'd22;
      3'd5: pow2 = 5'd24;
      3'd6: pow2 = 5'd26;
      3'd7: pow2 = 5'd29;
    endcase
    case (detune[1:0])
      2'd0: detune_limit = 5'd0;
      2'd1: detune_limit = 5'd8;
      2'd2: detune_limit = 5'd16;
      2'd3: detune_limit = 5'd22;
    endcase
    case (detune_kf[5:3])
      3'd0:   detune_unlimited = { 5'd0, pow2[4]   }; // <2
      3'd1:   detune_unlimited = { 4'd0, pow2[4:3] }; // <4
      3'd2:   detune_unlimited = { 3'd0, pow2[4:2] }; // <8
      3'd3:   detune_unlimited = { 2'd0, pow2[4:1] };
      3'd4:   detune_unlimited = { 1'd0, pow2[4:0] };
      3'd5:   detune_unlimited = { pow2[4:0], 1'd0 };
      default:detune_unlimited = 6'd0;
    endcase
    detune_limited = detune_unlimited > {1'b0, detune_limit} ? detune_limit : detune_unlimited[4:0];
    detune_signed = !detune[2] ? {1'b0, detune_limited} : (~{1'b0, detune_limited} + 6'd1);
  end

endmodule


///////////////////////////////////////////
// MODULE jt12_pg_inc
module jt12_pg_inc (
    input         [ 2:0] block,
    input         [10:0] fnum,
    input  signed [ 8:0] pm_offset,
    output reg    [16:0] phinc_pure
);

  reg [11:0] fnum_mod;

  always @(*) begin
    fnum_mod = {fnum, 1'b0} + {{3{pm_offset[8]}}, pm_offset};
    case (block)
      3'd0: phinc_pure = {7'd0, fnum_mod[11:2]};
      3'd1: phinc_pure = {6'd0, fnum_mod[11:1]};
      3'd2: phinc_pure = {5'd0, fnum_mod[11:0]};
      3'd3: phinc_pure = {4'd0, fnum_mod, 1'd0};
      3'd4: phinc_pure = {3'd0, fnum_mod, 2'd0};
      3'd5: phinc_pure = {2'd0, fnum_mod, 3'd0};
      3'd6: phinc_pure = {1'd0, fnum_mod, 4'd0};
      3'd7: phinc_pure = {fnum_mod, 5'd0};
    endcase
  end

endmodule


///////////////////////////////////////////
// MODULE jt12_pg_sum
module jt12_pg_sum (
    input        [ 3:0] mul,
    input        [19:0] phase_in,
    input               pg_rst,
    input signed [ 5:0] detune_signed,
    input        [16:0] phinc_pure,

    output reg [19:0] phase_out,
    output reg [ 9:0] phase_op
);

  reg [16:0] phinc_premul;
  reg [19:0] phinc_mul;

  always @(*) begin
    phinc_premul = phinc_pure + {{11{detune_signed[5]}}, detune_signed};
    phinc_mul    = (mul == 4'd0) ? {4'b0, phinc_premul[16:1]} : ({3'd0, phinc_premul} * mul);

    phase_out    = pg_rst ? 20'd0 : (phase_in + {phinc_mul});
    phase_op     = phase_out[19:10];
  end

endmodule


///////////////////////////////////////////
// MODULE jt12_pg_comb
module jt12_pg_comb (
    input [ 2:0] block,
    input [10:0] fnum,
    // Phase Modulation
    input [ 4:0] lfo_mod,
    input [ 2:0] pms,
    // output       [ 7:0]  pm_out,

    // Detune
    input [2:0] detune,

    output        [ 4:0] keycode,
    output signed [ 5:0] detune_out,
    // Phase increment  
    output        [16:0] phinc_out,
    // Phase add
    input         [ 3:0] mul,
    input         [19:0] phase_in,
    input                pg_rst,
    // input signed [7:0]   pm_in,
    input  signed [ 5:0] detune_in,
    input         [16:0] phinc_in,

    output [19:0] phase_out,
    output [ 9:0] phase_op
);

  wire signed [8:0] pm_offset;

  /*  pm, pg_dt and pg_inc operate in parallel */
  jt12_pm u_pm (
      .lfo_mod  (lfo_mod),
      .fnum     (fnum),
      .pms      (pms),
      .pm_offset(pm_offset)
  );

  jt12_pg_dt u_dt (
      .block        (block),
      .fnum         (fnum),
      .detune       (detune),
      .keycode      (keycode),
      .detune_signed(detune_out)
  );

  jt12_pg_inc u_inc (
      .block     (block),
      .fnum      (fnum),
      .pm_offset (pm_offset),
      .phinc_pure(phinc_out)
  );

  // pg_sum uses the output from the previous blocks

  jt12_pg_sum u_sum (
      .mul          (mul),
      .phase_in     (phase_in),
      .pg_rst       (pg_rst),
      .detune_signed(detune_in),
      .phinc_pure   (phinc_in),
      .phase_out    (phase_out),
      .phase_op     (phase_op)
  );

endmodule


///////////////////////////////////////////
// MODULE jt12_pg
module jt12_pg (
    input        clk,
    input        clk_en  /* synthesis direct_enable */,
    input        rst,
    // Channel frequency
    input [10:0] fnum_I,
    input [ 2:0] block_I,
    // Operator multiplying
    input [ 3:0] mul_II,
    // Operator detuning
    input [ 2:0] dt1_I,                                  // same as JT51's DT1
    // phase modulation from LFO
    input [ 6:0] lfo_mod,
    input [ 2:0] pms_I,
    // phase operation
    input        pg_rst_II,
    input        pg_stop,                                // not implemented

    output reg   [ 4:0] keycode_II,
    output       [ 9:0] phase_VIII,
    input               auto_ss_rd,
    input               auto_ss_wr,
    input        [31:0] auto_ss_data_in,
    input        [ 7:0] auto_ss_device_idx,
    input        [15:0] auto_ss_state_idx,
    input        [ 7:0] auto_ss_base_device_idx,
    output logic [31:0] auto_ss_data_out,
    output logic        auto_ss_ack

);
  assign auto_ss_ack = auto_ss_local_ack | auto_ss_u_phsh_ack | auto_ss_u_pad_ack;

  assign auto_ss_data_out = auto_ss_local_data_out | auto_ss_u_phsh_data_out | auto_ss_u_pad_data_out;

  logic        auto_ss_local_ack;

  logic [31:0] auto_ss_local_data_out;

  wire         auto_ss_u_pad_ack;

  wire  [31:0] auto_ss_u_pad_data_out;

  wire         auto_ss_u_phsh_ack;

  wire  [31:0] auto_ss_u_phsh_data_out;

  wire         device_match = (auto_ss_device_idx == auto_ss_base_device_idx);

  genvar auto_ss_idx;


  parameter num_ch = 6;

  wire        [ 4:0] keycode_I;
  wire signed [ 5:0] detune_mod_I;
  reg signed  [ 5:0] detune_mod_II;
  wire        [16:0] phinc_I;
  reg         [16:0] phinc_II;
  wire [19:0] phase_drop, phase_in;
  wire [9:0] phase_II;

  always @(posedge clk) begin
    if (clk_en) begin
      keycode_II    <= keycode_I;
      detune_mod_II <= detune_mod_I;
      phinc_II      <= phinc_I;
    end
    if (auto_ss_wr && device_match) begin
      case (auto_ss_state_idx)
        0: begin
          phinc_II      <= auto_ss_data_in[16:0];
          detune_mod_II <= auto_ss_data_in[22:17];
          keycode_II    <= auto_ss_data_in[27:23];
        end
        default: begin
        end
      endcase
    end
  end


  always_comb begin
    auto_ss_local_data_out = 32'h0;
    auto_ss_local_ack      = 1'b0;
    if (auto_ss_rd && device_match) begin
      case (auto_ss_state_idx)
        0: begin
          auto_ss_local_data_out[27:0] = {keycode_II, detune_mod_II, phinc_II};
          auto_ss_local_ack            = 1'b1;
        end
        default: begin
        end
      endcase
    end
  end



  jt12_pg_comb u_comb (
      .block  (block_I),
      .fnum   (fnum_I),
      // Phase Modulation
      .lfo_mod(lfo_mod[6:2]),
      .pms    (pms_I),

      // Detune
      .detune    (dt1_I),
      .keycode   (keycode_I),
      .detune_out(detune_mod_I),
      // Phase increment  
      .phinc_out (phinc_I),
      // Phase add
      .mul       (mul_II),
      .phase_in  (phase_drop),
      .pg_rst    (pg_rst_II),
      .detune_in (detune_mod_II),
      .phinc_in  (phinc_II),

      .phase_out(phase_in),
      .phase_op (phase_II)
  );

  jt12_sh_rst #(
      .width (20),
      .stages(4 * num_ch)
  ) u_phsh (
      .clk                    (clk),
      .clk_en                 (clk_en),
      .rst                    (rst),
      .din                    (phase_in),
      .drop                   (phase_drop),
      .auto_ss_rd             (auto_ss_rd),
      .auto_ss_wr             (auto_ss_wr),
      .auto_ss_data_in        (auto_ss_data_in),
      .auto_ss_device_idx     (auto_ss_device_idx),
      .auto_ss_state_idx      (auto_ss_state_idx),
      .auto_ss_base_device_idx(auto_ss_base_device_idx + 1),
      .auto_ss_data_out       (auto_ss_u_phsh_data_out),
      .auto_ss_ack            (auto_ss_u_phsh_ack)

  );

  jt12_sh_rst #(
      .width (10),
      .stages(6)
  ) u_pad (
      .clk                    (clk),
      .clk_en                 (clk_en),
      .rst                    (rst),
      .din                    (phase_II),
      .drop                   (phase_VIII),
      .auto_ss_rd             (auto_ss_rd),
      .auto_ss_wr             (auto_ss_wr),
      .auto_ss_data_in        (auto_ss_data_in),
      .auto_ss_device_idx     (auto_ss_device_idx),
      .auto_ss_state_idx      (auto_ss_state_idx),
      .auto_ss_base_device_idx(auto_ss_base_device_idx + 2),
      .auto_ss_data_out       (auto_ss_u_pad_data_out),
      .auto_ss_ack            (auto_ss_u_pad_ack)

  );

endmodule


///////////////////////////////////////////
// MODULE jt12_eg_cnt
module jt12_eg_cnt (
    input               rst,
    input               clk,
    input               clk_en  /* synthesis direct_enable */,
    input               zero,
    output reg   [14:0] eg_cnt,
    input               auto_ss_rd,
    input               auto_ss_wr,
    input        [31:0] auto_ss_data_in,
    input        [ 7:0] auto_ss_device_idx,
    input        [15:0] auto_ss_state_idx,
    input        [ 7:0] auto_ss_base_device_idx,
    output logic [31:0] auto_ss_data_out,
    output logic        auto_ss_ack

);
  wire device_match = (auto_ss_device_idx == auto_ss_base_device_idx);

  genvar auto_ss_idx;


  reg [1:0] eg_cnt_base;

  always @(posedge clk, posedge rst) begin : envelope_counter
    if (rst) begin
      eg_cnt_base <= 2'd0;
      eg_cnt      <= 15'd0;
    end else if (auto_ss_wr && device_match) begin
      case (auto_ss_state_idx)
        0: begin
          eg_cnt      <= auto_ss_data_in[14:0];
          eg_cnt_base <= auto_ss_data_in[16:15];
        end
        default: begin
        end
      endcase
    end else begin
      if (zero && clk_en) begin
        // envelope counter increases every 3 output samples,
        // there is one sample every 24 clock ticks
        if (eg_cnt_base == 2'd2) begin
          eg_cnt      <= eg_cnt + 1'b1;
          eg_cnt_base <= 2'd0;
        end else eg_cnt_base <= eg_cnt_base + 1'b1;
      end
    end
  end
  always_comb begin
    auto_ss_data_out = 32'h0;
    auto_ss_ack      = 1'b0;
    if (auto_ss_rd && device_match) begin
      case (auto_ss_state_idx)
        0: begin
          auto_ss_data_out[16:0] = {eg_cnt_base, eg_cnt};
          auto_ss_ack            = 1'b1;
        end
        default: begin
        end
      endcase
    end
  end



endmodule


///////////////////////////////////////////
// MODULE jt12_eg_ctrl
module jt12_eg_ctrl (
    input            keyon_now,
    input            keyoff_now,
    input      [2:0] state_in,
    input      [9:0] eg,
    // envelope configuration
    input      [4:0] arate,       // attack  rate
    input      [4:0] rate1,       // decay   rate
    input      [4:0] rate2,       // sustain rate
    input      [3:0] rrate,
    input      [3:0] sl,          // sustain level
    // SSG operation
    input            ssg_en,
    input      [2:0] ssg_eg,
    // SSG output inversion
    input            ssg_inv_in,
    output reg       ssg_inv_out,

    output reg [4:0] base_rate,
    output reg [2:0] state_next,
    output reg       pg_rst
);

  localparam 	ATTACK = 3'b001,
			DECAY  = 3'b010,
			HOLD   = 3'b100,
			RELEASE= 3'b000; // default state is release

  // wire is_decaying = state_in[1] | state_in[2];

  reg [4:0] sustain;

  always @(*)
    if (sl == 4'd15) sustain = 5'h1f;  // 93dB
    else sustain = {1'b0, sl};

  wire ssg_en_out;
  reg ssg_en_in, ssg_pg_rst;

  // aliases
  wire ssg_att = ssg_eg[2];
  wire ssg_alt = ssg_eg[1];
  wire ssg_hold = ssg_eg[0] & ssg_en;

  reg  ssg_over;


  always @(*) begin
    ssg_over   = ssg_en && eg[9];  // eg >=10'h200
    ssg_pg_rst = ssg_over && !(ssg_alt || ssg_hold);
    pg_rst     = keyon_now | ssg_pg_rst;
  end

  always @(*)
    casez ({
      keyoff_now, keyon_now, state_in
    })
      5'b01_???: begin  // key on
        base_rate   = arate;
        state_next  = ATTACK;
        ssg_inv_out = ssg_att & ssg_en;
      end
      {
        2'b00, ATTACK
      } :
      if (eg == 10'd0) begin
        base_rate   = rate1;
        state_next  = DECAY;
        ssg_inv_out = ssg_inv_in;
      end else begin
        base_rate   = arate;
        state_next  = ATTACK;
        ssg_inv_out = ssg_inv_in;
      end
      {
        2'b00, DECAY
      } : begin
        if (ssg_over) begin
          base_rate   = ssg_hold ? 5'd0 : arate;
          state_next  = ssg_hold ? HOLD : ATTACK;
          ssg_inv_out = ssg_en & (ssg_alt ^ ssg_inv_in);
        end else begin
          base_rate   = eg[9:5] >= sustain ? rate2 : rate1;  // equal comparison according to Nuke
          state_next  = DECAY;
          ssg_inv_out = ssg_inv_in;
        end
      end
      {
        2'b00, HOLD
      } : begin
        base_rate   = 5'd0;
        state_next  = HOLD;
        ssg_inv_out = ssg_inv_in;
      end
      default: begin  // RELEASE, note that keyoff_now==1 will enter this state too
        base_rate   = {rrate, 1'b1};
        state_next  = RELEASE;  // release
        ssg_inv_out = 1'b0;  // this can produce a glitch in the output
        // But to release from SSG cannot be done nicely while
        // inverting the ouput
      end
    endcase


endmodule


///////////////////////////////////////////
// MODULE jt12_eg_step
module jt12_eg_step (
    input             attack,
    input      [ 4:0] base_rate,
    input      [ 4:0] keycode,
    input      [14:0] eg_cnt,
    input             cnt_in,
    input      [ 1:0] ks,
    output            cnt_lsb,
    output reg        step,
    output reg [ 5:0] rate,
    output reg        sum_up
);

  reg [6:0] pre_rate;

  always @(*) begin : pre_rate_calc
    if (base_rate == 5'd0) pre_rate = 7'd0;
    else
      case (ks)
        2'd3: pre_rate = {base_rate, 1'b0} + {1'b0, keycode};
        2'd2: pre_rate = {base_rate, 1'b0} + {2'b0, keycode[4:1]};
        2'd1: pre_rate = {base_rate, 1'b0} + {3'b0, keycode[4:2]};
        2'd0: pre_rate = {base_rate, 1'b0} + {4'b0, keycode[4:3]};
      endcase
  end

  always @(*) rate = pre_rate[6] ? 6'd63 : pre_rate[5:0];

  reg [2:0] cnt;

  reg [4:0] mux_sel;
  always @(*) begin
    mux_sel = attack ? (rate[5:2] + 4'd1) : {1'b0, rate[5:2]};
  end  // always @(*)

  always @(*)
    case (mux_sel)
      5'h0: cnt = eg_cnt[14:12];
      5'h1: cnt = eg_cnt[13:11];
      5'h2: cnt = eg_cnt[12:10];
      5'h3: cnt = eg_cnt[11:9];
      5'h4: cnt = eg_cnt[10:8];
      5'h5: cnt = eg_cnt[9:7];
      5'h6: cnt = eg_cnt[8:6];
      5'h7: cnt = eg_cnt[7:5];
      5'h8: cnt = eg_cnt[6:4];
      5'h9: cnt = eg_cnt[5:3];
      5'ha: cnt = eg_cnt[4:2];
      5'hb: cnt = eg_cnt[3:1];
      default: cnt = eg_cnt[2:0];
    endcase

  ////////////////////////////////
  reg [7:0] step_idx;

  always @(*) begin : rate_step
    if (rate[5:4] == 2'b11) begin  // 0 means 1x, 1 means 2x
      if (rate[5:2] == 4'hf && attack) step_idx = 8'b11111111;  // Maximum attack speed, rates 60&61
      else
        case (rate[1:0])
          2'd0: step_idx = 8'b00000000;
          2'd1: step_idx = 8'b10001000;  // 2
          2'd2: step_idx = 8'b10101010;  // 4
          2'd3: step_idx = 8'b11101110;  // 6
        endcase
    end else begin
      if (rate[5:2] == 4'd0 && !attack) step_idx = 8'b11111110;  // limit slowest decay rate
      else
        case (rate[1:0])
          2'd0: step_idx = 8'b10101010;  // 4
          2'd1: step_idx = 8'b11101010;  // 5
          2'd2: step_idx = 8'b11101110;  // 6
          2'd3: step_idx = 8'b11111110;  // 7
        endcase
    end
    // a rate of zero keeps the level still
    step = rate[5:1] == 5'd0 ? 1'b0 : step_idx[cnt];
  end

  assign cnt_lsb = cnt[0];
  always @(*) begin
    sum_up = cnt[0] != cnt_in;
  end

endmodule


///////////////////////////////////////////
// MODULE jt12_eg_pure
module jt12_eg_pure (
    input            attack,
    input            step,
    input      [5:1] rate,
    input      [9:0] eg_in,
    input            ssg_en,
    input            sum_up,
    output reg [9:0] eg_pure
);

  reg [ 3:0] dr_sum;
  reg [ 9:0] dr_adj;
  reg [10:0] dr_result;

  always @(*) begin : dr_calculation
    case (rate[5:2])
      4'b1100: dr_sum = {2'b0, step, ~step};  // 12
      4'b1101: dr_sum = {1'b0, step, ~step, 1'b0};  // 13
      4'b1110: dr_sum = {step, ~step, 2'b0};  // 14
      4'b1111: dr_sum = 4'd8;  // 15
      default: dr_sum = {2'b0, step, 1'b0};
    endcase
    // Decay rate attenuation is multiplied by 4 for SSG operation
    dr_adj    = ssg_en ? {4'd0, dr_sum, 2'd0} : {6'd0, dr_sum};
    dr_result = dr_adj + eg_in;
  end

  reg [ 7:0] ar_sum0;
  reg [ 8:0] ar_sum1;
  reg [10:0] ar_result;
  reg [ 9:0] ar_sum;

  always @(*) begin : ar_calculation
    casez (rate[5:2])
      default: ar_sum0 = {2'd0, eg_in[9:4]};
      4'b1101: ar_sum0 = {1'd0, eg_in[9:3]};
      4'b111?: ar_sum0 = eg_in[9:2];
    endcase
    ar_sum1 = ar_sum0 + 9'd1;
    if (rate[5:4] == 2'b11) ar_sum = step ? {ar_sum1, 1'b0} : {1'b0, ar_sum1};
    else ar_sum = step ? {1'b0, ar_sum1} : 10'd0;
    ar_result = eg_in - ar_sum;
  end
  ///////////////////////////////////////////////////////////
  // rate not used below this point
  reg [9:0] eg_pre_fastar;  // pre fast attack rate
  always @(*) begin
    if (sum_up) begin
      if (attack) eg_pre_fastar = ar_result[10] ? 10'd0 : ar_result[9:0];
      else eg_pre_fastar = dr_result[10] ? 10'h3FF : dr_result[9:0];
    end else eg_pre_fastar = eg_in;
    eg_pure = (attack & rate[5:1] == 5'h1F) ? 10'd0 : eg_pre_fastar;
  end

endmodule


///////////////////////////////////////////
// MODULE jt12_eg_final
module jt12_eg_final (
    input      [6:0] lfo_mod,
    input            amsen,
    input      [1:0] ams,
    input      [6:0] tl,
    input      [9:0] eg_pure_in,
    input            ssg_inv,
    output reg [9:0] eg_limited
);

  reg [ 8:0] am_final;
  reg [11:0] sum_eg_tl;
  reg [11:0] sum_eg_tl_am;
  reg [ 5:0] am_inverted;
  reg [ 9:0] eg_pream;

  always @(*) begin
    am_inverted = lfo_mod[6] ? ~lfo_mod[5:0] : lfo_mod[5:0];
  end

  always @(*) begin
    casez ({
      amsen, ams
    })
      default: am_final = 9'd0;
      3'b1_01: am_final = {5'd0, am_inverted[5:2]};
      3'b1_10: am_final = {3'd0, am_inverted};
      3'b1_11: am_final = {2'd0, am_inverted, 1'b0};
    endcase
    eg_pream = ssg_inv ? (10'h200 - eg_pure_in) : eg_pure_in;
    sum_eg_tl = {1'b0, tl, 3'd0} + {1'b0, eg_pream};  // leading zeros needed to compute correctly
    sum_eg_tl_am = sum_eg_tl + {3'd0, am_final};
  end

  always @(*) eg_limited = sum_eg_tl_am[11:10] == 2'd0 ? sum_eg_tl_am[9:0] : 10'h3ff;

endmodule


///////////////////////////////////////////
// MODULE jt12_eg_comb
module jt12_eg_comb (
    input        keyon_now,
    input        keyoff_now,
    input  [2:0] state_in,
    input  [9:0] eg_in,
    // envelope configuration   
    input  [4:0] arate,       // attack  rate
    input  [4:0] rate1,       // decay   rate
    input  [4:0] rate2,       // sustain rate
    input  [3:0] rrate,
    input  [3:0] sl,          // sustain level
    // SSG operation
    input        ssg_en,
    input  [2:0] ssg_eg,
    // SSG output inversion
    input        ssg_inv_in,
    output       ssg_inv_out,

    output [ 4:0] base_rate,
    output [ 2:0] state_next,
    output        pg_rst,
    ///////////////////////////////////
    // II
    input         step_attack,
    input  [ 4:0] step_rate_in,
    input  [ 4:0] keycode,
    input  [14:0] eg_cnt,
    input         cnt_in,
    input  [ 1:0] ks,
    output        cnt_lsb,
    output        step,
    output [ 5:0] step_rate_out,
    output        sum_up_out,
    ///////////////////////////////////
    // III
    input         pure_attack,
    input         pure_step,
    input  [ 5:1] pure_rate,
    input         pure_ssg_en,
    input  [ 9:0] pure_eg_in,
    output [ 9:0] pure_eg_out,
    input         sum_up_in,
    ///////////////////////////////////
    // IV
    input  [ 6:0] lfo_mod,
    input         amsen,
    input  [ 1:0] ams,
    input  [ 6:0] tl,
    input  [ 9:0] final_eg_in,
    input         final_ssg_inv,
    output [ 9:0] final_eg_out
);

  // I
  jt12_eg_ctrl u_ctrl (
      .keyon_now  (keyon_now),
      .keyoff_now (keyoff_now),
      .state_in   (state_in),
      .eg         (eg_in),
      // envelope configuration   
      .arate      (arate),       // attack  rate
      .rate1      (rate1),       // decay   rate
      .rate2      (rate2),       // sustain rate
      .rrate      (rrate),
      .sl         (sl),          // sustain level
      // SSG operation
      .ssg_en     (ssg_en),
      .ssg_eg     (ssg_eg),
      // SSG output inversion
      .ssg_inv_in (ssg_inv_in),
      .ssg_inv_out(ssg_inv_out),

      .base_rate (base_rate),
      .state_next(state_next),
      .pg_rst    (pg_rst)
  );

  // II

  jt12_eg_step u_step (
      .attack   (step_attack),
      .base_rate(step_rate_in),
      .keycode  (keycode),
      .eg_cnt   (eg_cnt),
      .cnt_in   (cnt_in),
      .ks       (ks),
      .cnt_lsb  (cnt_lsb),
      .step     (step),
      .rate     (step_rate_out),
      .sum_up   (sum_up_out)
  );

  // III

  wire [9:0] egin, egout;
  jt12_eg_pure u_pure (
      .attack (pure_attack),
      .step   (pure_step),
      .rate   (pure_rate),
      .ssg_en (pure_ssg_en),
      .eg_in  (pure_eg_in),
      .eg_pure(pure_eg_out),
      .sum_up (sum_up_in)
  );

  // IV

  jt12_eg_final u_final (
      .lfo_mod   (lfo_mod),
      .amsen     (amsen),
      .ams       (ams),
      .tl        (tl),
      .ssg_inv   (final_ssg_inv),
      .eg_pure_in(final_eg_in),
      .eg_limited(final_eg_out)
  );

endmodule


///////////////////////////////////////////
// MODULE jt12_sh
module jt12_sh #(
    parameter width  = 5,
              stages = 24
) (
    input                    clk,
    input                    clk_en  /* synthesis direct_enable */,
    input        [width-1:0] din,
    output       [width-1:0] drop,
    input                    auto_ss_rd,
    input                    auto_ss_wr,
    input        [     31:0] auto_ss_data_in,
    input        [      7:0] auto_ss_device_idx,
    input        [     15:0] auto_ss_state_idx,
    input        [      7:0] auto_ss_base_device_idx,
    output logic [     31:0] auto_ss_data_out,
    output logic             auto_ss_ack

);
  wire device_match = (auto_ss_device_idx == auto_ss_base_device_idx);

  genvar auto_ss_idx;


  reg [stages-1:0] bits[width-1:0];

  always @(posedge clk) begin
    begin
      if (clk_en) begin
        for (int i = 0; i < width; i = i + 1) begin
          bits[i] <= {bits[i][stages-2:0], din[i]};
        end
      end
    end
    if (auto_ss_wr && device_match) begin
      if (auto_ss_state_idx < (width)) begin
        bits[auto_ss_state_idx] <= auto_ss_data_in[stages-1:0];
      end
    end
  end


  always_comb begin
    auto_ss_data_out = 32'h0;
    auto_ss_ack      = 1'b0;
    if (auto_ss_rd && device_match) begin
      if (auto_ss_state_idx < (width)) begin
        auto_ss_data_out[stages-1:0] = bits[auto_ss_state_idx];
        auto_ss_ack                  = 1'b1;
      end
    end
  end




  genvar i;
  generate
    for (i = 0; i < width; i = i + 1) begin : bit_shifter
      assign drop[i] = bits[i][stages-1];
    end
  endgenerate

endmodule


///////////////////////////////////////////
// MODULE jt12_eg
module jt12_eg (
    input       rst,
    input       clk,
    input       clk_en  /* synthesis direct_enable */,
    input       zero,
    input       eg_stop,
    // envelope configuration
    input [4:0] keycode_II,
    input [4:0] arate_I,                                // attack  rate
    input [4:0] rate1_I,                                // decay   rate
    input [4:0] rate2_I,                                // sustain rate
    input [3:0] rrate_I,                                // release rate
    input [3:0] sl_I,                                   // sustain level
    input [1:0] ks_II,                                  // key scale
    // SSG operation
    input       ssg_en_I,
    input [2:0] ssg_eg_I,
    // envelope operation
    input       keyon_I,
    // envelope number
    input [6:0] lfo_mod,
    input       amsen_IV,
    input [1:0] ams_IV,
    input [6:0] tl_IV,

    output reg   [ 9:0] eg_V,
    output reg          pg_rst_II,
    input               auto_ss_rd,
    input               auto_ss_wr,
    input        [31:0] auto_ss_data_in,
    input        [ 7:0] auto_ss_device_idx,
    input        [15:0] auto_ss_state_idx,
    input        [ 7:0] auto_ss_base_device_idx,
    output logic [31:0] auto_ss_data_out,
    output logic        auto_ss_ack

);
  assign auto_ss_ack = auto_ss_local_ack | auto_ss_u_egcnt_ack | auto_ss_u_cntsh_ack | auto_ss_u_egsh_ack | auto_ss_u_egstate_ack | auto_ss_u_ssg_inv_ack | auto_ss_u_konsh_ack;

  assign auto_ss_data_out = auto_ss_local_data_out | auto_ss_u_egcnt_data_out | auto_ss_u_cntsh_data_out | auto_ss_u_egsh_data_out | auto_ss_u_egstate_data_out | auto_ss_u_ssg_inv_data_out | auto_ss_u_konsh_data_out;

  logic        auto_ss_local_ack;

  logic [31:0] auto_ss_local_data_out;

  wire         auto_ss_u_konsh_ack;

  wire  [31:0] auto_ss_u_konsh_data_out;

  wire         auto_ss_u_ssg_inv_ack;

  wire  [31:0] auto_ss_u_ssg_inv_data_out;

  wire         auto_ss_u_egstate_ack;

  wire  [31:0] auto_ss_u_egstate_data_out;

  wire         auto_ss_u_egsh_ack;

  wire  [31:0] auto_ss_u_egsh_data_out;

  wire         auto_ss_u_cntsh_ack;

  wire  [31:0] auto_ss_u_cntsh_data_out;

  wire         auto_ss_u_egcnt_ack;

  wire  [31:0] auto_ss_u_egcnt_data_out;

  wire         device_match = (auto_ss_device_idx == auto_ss_base_device_idx);

  genvar auto_ss_idx;


  parameter num_ch = 6;

  wire [14:0] eg_cnt;

  jt12_eg_cnt u_egcnt (
      .rst                    (rst),
      .clk                    (clk),
      .clk_en                 (clk_en & ~eg_stop),
      .zero                   (zero),
      .eg_cnt                 (eg_cnt),
      .auto_ss_rd             (auto_ss_rd),
      .auto_ss_wr             (auto_ss_wr),
      .auto_ss_data_in        (auto_ss_data_in),
      .auto_ss_device_idx     (auto_ss_device_idx),
      .auto_ss_state_idx      (auto_ss_state_idx),
      .auto_ss_base_device_idx(auto_ss_base_device_idx + 1),
      .auto_ss_data_out       (auto_ss_u_egcnt_data_out),
      .auto_ss_ack            (auto_ss_u_egcnt_ack)

  );

  wire keyon_last_I;
  wire keyon_now_I = !keyon_last_I && keyon_I;
  wire keyoff_now_I = keyon_last_I && !keyon_I;

  wire cnt_in_II, cnt_lsb_II, step_II, pg_rst_I;

  wire ssg_inv_in_I, ssg_inv_out_I;
  reg ssg_inv_II, ssg_inv_III, ssg_inv_IV;
  wire [2:0] state_in_I, state_next_I;

  reg attack_II, attack_III;
  wire [4:0] base_rate_I;
  reg  [4:0] base_rate_II;
  wire [5:0] rate_out_II;
  reg  [5:1] rate_in_III;
  reg step_III, ssg_en_II, ssg_en_III;
  wire sum_out_II;
  reg  sum_in_III;

  wire [9:0] eg_in_I, pure_eg_out_III, eg_next_III, eg_out_IV;
  reg [9:0] eg_in_II, eg_in_III, eg_in_IV;



  jt12_eg_comb u_comb (
      ///////////////////////////////////
      // I
      .keyon_now  (keyon_now_I),
      .keyoff_now (keyoff_now_I),
      .state_in   (state_in_I),
      .eg_in      (eg_in_I),
      // envelope configuration   
      .arate      (arate_I),       // attack  rate
      .rate1      (rate1_I),       // decay   rate
      .rate2      (rate2_I),       // sustain rate
      .rrate      (rrate_I),
      .sl         (sl_I),          // sustain level
      // SSG operation
      .ssg_en     (ssg_en_I),
      .ssg_eg     (ssg_eg_I),
      // SSG output inversion
      .ssg_inv_in (ssg_inv_in_I),
      .ssg_inv_out(ssg_inv_out_I),

      .base_rate    (base_rate_I),
      .state_next   (state_next_I),
      .pg_rst       (pg_rst_I),
      ///////////////////////////////////
      // II
      .step_attack  (attack_II),
      .step_rate_in (base_rate_II),
      .keycode      (keycode_II),
      .eg_cnt       (eg_cnt),
      .cnt_in       (cnt_in_II),
      .ks           (ks_II),
      .cnt_lsb      (cnt_lsb_II),
      .step         (step_II),
      .step_rate_out(rate_out_II),
      .sum_up_out   (sum_out_II),
      ///////////////////////////////////
      // III
      .pure_attack  (attack_III),
      .pure_step    (step_III),
      .pure_rate    (rate_in_III[5:1]),
      .pure_ssg_en  (ssg_en_III),
      .pure_eg_in   (eg_in_III),
      .pure_eg_out  (pure_eg_out_III),
      .sum_up_in    (sum_in_III),
      ///////////////////////////////////
      // IV
      .lfo_mod      (lfo_mod),
      .amsen        (amsen_IV),
      .ams          (ams_IV),
      .tl           (tl_IV),
      .final_ssg_inv(ssg_inv_IV),
      .final_eg_in  (eg_in_IV),
      .final_eg_out (eg_out_IV)
  );

  always @(posedge clk) begin
    if (clk_en) begin
      eg_in_II     <= eg_in_I;
      attack_II    <= state_next_I[0];
      base_rate_II <= base_rate_I;
      ssg_en_II    <= ssg_en_I;
      ssg_inv_II   <= ssg_inv_out_I;
      pg_rst_II    <= pg_rst_I;

      eg_in_III    <= eg_in_II;
      attack_III   <= attack_II;
      rate_in_III  <= rate_out_II[5:1];
      ssg_en_III   <= ssg_en_II;
      ssg_inv_III  <= ssg_inv_II;
      step_III     <= step_II;
      sum_in_III   <= sum_out_II;

      ssg_inv_IV   <= ssg_inv_III;
      eg_in_IV     <= pure_eg_out_III;
      eg_V         <= eg_out_IV;
    end
    if (auto_ss_wr && device_match) begin
      case (auto_ss_state_idx)
        0: begin
          eg_V      <= auto_ss_data_in[9:0];
          eg_in_II  <= auto_ss_data_in[19:10];
          eg_in_III <= auto_ss_data_in[29:20];
        end
        1: begin
          eg_in_IV     <= auto_ss_data_in[9:0];
          base_rate_II <= auto_ss_data_in[14:10];
          rate_in_III  <= auto_ss_data_in[19:15];
          attack_II    <= auto_ss_data_in[20];
          attack_III   <= auto_ss_data_in[21];
          pg_rst_II    <= auto_ss_data_in[22];
          ssg_en_II    <= auto_ss_data_in[23];
          ssg_en_III   <= auto_ss_data_in[24];
          ssg_inv_II   <= auto_ss_data_in[25];
          ssg_inv_III  <= auto_ss_data_in[26];
          ssg_inv_IV   <= auto_ss_data_in[27];
          step_III     <= auto_ss_data_in[28];
          sum_in_III   <= auto_ss_data_in[29];
        end
        default: begin
        end
      endcase
    end
  end


  always_comb begin
    auto_ss_local_data_out = 32'h0;
    auto_ss_local_ack      = 1'b0;
    if (auto_ss_rd && device_match) begin
      case (auto_ss_state_idx)
        0: begin
          auto_ss_local_data_out[29:0] = {eg_in_III, eg_in_II, eg_V};
          auto_ss_local_ack            = 1'b1;
        end
        1: begin
          auto_ss_local_data_out[29:0] = {
            sum_in_III,
            step_III,
            ssg_inv_IV,
            ssg_inv_III,
            ssg_inv_II,
            ssg_en_III,
            ssg_en_II,
            pg_rst_II,
            attack_III,
            attack_II,
            rate_in_III,
            base_rate_II,
            eg_in_IV
          };
          auto_ss_local_ack = 1'b1;
        end
        default: begin
        end
      endcase
    end
  end



  jt12_sh #(
      .width (1),
      .stages(4 * num_ch)
  ) u_cntsh (
      .clk                    (clk),
      .clk_en                 (clk_en),
      .din                    (cnt_lsb_II),
      .drop                   (cnt_in_II),
      .auto_ss_rd             (auto_ss_rd),
      .auto_ss_wr             (auto_ss_wr),
      .auto_ss_data_in        (auto_ss_data_in),
      .auto_ss_device_idx     (auto_ss_device_idx),
      .auto_ss_state_idx      (auto_ss_state_idx),
      .auto_ss_base_device_idx(auto_ss_base_device_idx + 2),
      .auto_ss_data_out       (auto_ss_u_cntsh_data_out),
      .auto_ss_ack            (auto_ss_u_cntsh_ack)

  );

  jt12_sh_rst #(
      .width (10),
      .stages(4 * num_ch - 3),
      .rstval(1'b1)
  ) u_egsh (
      .clk                    (clk),
      .clk_en                 (clk_en),
      .rst                    (rst),
      .din                    (eg_in_IV),
      .drop                   (eg_in_I),
      .auto_ss_rd             (auto_ss_rd),
      .auto_ss_wr             (auto_ss_wr),
      .auto_ss_data_in        (auto_ss_data_in),
      .auto_ss_device_idx     (auto_ss_device_idx),
      .auto_ss_state_idx      (auto_ss_state_idx),
      .auto_ss_base_device_idx(auto_ss_base_device_idx + 3),
      .auto_ss_data_out       (auto_ss_u_egsh_data_out),
      .auto_ss_ack            (auto_ss_u_egsh_ack)

  );

  jt12_sh_rst #(
      .width (3),
      .stages(4 * num_ch),
      .rstval(1'b1)
  ) u_egstate (
      .clk                    (clk),
      .clk_en                 (clk_en),
      .rst                    (rst),
      .din                    (state_next_I),
      .drop                   (state_in_I),
      .auto_ss_rd             (auto_ss_rd),
      .auto_ss_wr             (auto_ss_wr),
      .auto_ss_data_in        (auto_ss_data_in),
      .auto_ss_device_idx     (auto_ss_device_idx),
      .auto_ss_state_idx      (auto_ss_state_idx),
      .auto_ss_base_device_idx(auto_ss_base_device_idx + 4),
      .auto_ss_data_out       (auto_ss_u_egstate_data_out),
      .auto_ss_ack            (auto_ss_u_egstate_ack)

  );

  jt12_sh_rst #(
      .width (1),
      .stages(4 * num_ch - 3),
      .rstval(1'b0)
  ) u_ssg_inv (
      .clk                    (clk),
      .clk_en                 (clk_en),
      .rst                    (rst),
      .din                    (ssg_inv_IV),
      .drop                   (ssg_inv_in_I),
      .auto_ss_rd             (auto_ss_rd),
      .auto_ss_wr             (auto_ss_wr),
      .auto_ss_data_in        (auto_ss_data_in),
      .auto_ss_device_idx     (auto_ss_device_idx),
      .auto_ss_state_idx      (auto_ss_state_idx),
      .auto_ss_base_device_idx(auto_ss_base_device_idx + 5),
      .auto_ss_data_out       (auto_ss_u_ssg_inv_data_out),
      .auto_ss_ack            (auto_ss_u_ssg_inv_ack)

  );

  jt12_sh_rst #(
      .width (1),
      .stages(4 * num_ch),
      .rstval(1'b0)
  ) u_konsh (
      .clk                    (clk),
      .clk_en                 (clk_en),
      .rst                    (rst),
      .din                    (keyon_I),
      .drop                   (keyon_last_I),
      .auto_ss_rd             (auto_ss_rd),
      .auto_ss_wr             (auto_ss_wr),
      .auto_ss_data_in        (auto_ss_data_in),
      .auto_ss_device_idx     (auto_ss_device_idx),
      .auto_ss_state_idx      (auto_ss_state_idx),
      .auto_ss_base_device_idx(auto_ss_base_device_idx + 6),
      .auto_ss_data_out       (auto_ss_u_konsh_data_out),
      .auto_ss_ack            (auto_ss_u_konsh_ack)

  );


endmodule
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
