wickerwaka/Arcade-IGSPGM_MiSTer/rtl/igs023_bg.sv

module IGS023_BG(
    input clk,
    input ce_pixel,

    input start_read,
    input scan_active,

    input [10:0] x,
    input [10:0] y,
    input [7:0] screen_y,

    output [9:0] color_out,

    input [31:0] scale_bits_x,
    input [31:0] scale_bits_y,
    input        zoom_mode_x,
    input        zoom_mode_y,

    // VRAM interface
    output logic [14:0] vram_addr,
    input        [7:0]  vram_din,
    output              vram_master,
    
    // ROM interface
    output reg [23:0] rom_address,
    input      [31:0] rom_data,
    output reg        rom_req,
    input             rom_ack
);


reg [4:0] buffer[32];
reg [4:0] pal_buffer[32];

reg [31:0] scale_shifter_x;

reg load_buffer;
reg [31:0] stage_data;
reg [2:0] load_slot;

logic [8:0] slot_increment[5] = '{ 6, 6, 7, 6, 7 };
reg [8:0] pixel_in_idx, pixel_out_idx;

wire buffer_ready = (slot_increment[load_slot] + pixel_in_idx) < pixel_out_idx;

typedef enum logic[4:0] {
    READ_SCROLL0, READ_SCROLL1, READ_SCROLL2, APPLY_SCROLL,
    READ0, READ1, READ2, READ3, READ4, READ5, READ6,
    ROM_REQ0, ROM_WAIT0,
    ROM_WAIT1,
    ROM_WAIT2,
    ROM_WAIT3,
    ROM_WAIT4,
    DONE
} state_t;

state_t state = DONE;

reg toggle = 0;
assign vram_master = (state <= READ3);

reg [14:0] scroll_addr;
reg [15:0] scroll;
reg [6:0] vram_row_addr;
reg [7:0] tile_addr;

wire [10:0] scrolled_x = x + scroll[10:0];

reg [15:0] tile_code;
reg [7:0] tile_attrib;
wire flip_y = tile_attrib[7];
wire flip_x = tile_attrib[6];

function automatic [4:0] stream5(input [5:0] base);
begin
    stream5 = flip_x ? stage_data[31 - base -: 5] : stage_data[base +: 5];
end
endfunction

function automatic [3:0] stream4(input [5:0] base);
begin
    stream4 = flip_x ? stage_data[31 - base -: 4] : stage_data[base +: 4];
end
endfunction

function automatic [2:0] stream3(input [5:0] base);
begin
    stream3 = flip_x ? stage_data[31 - base -: 3] : stage_data[base +: 3];
end
endfunction

function automatic [1:0] stream2(input [5:0] base);
begin
    stream2 = flip_x ? stage_data[31 - base -: 2] : stage_data[base +: 2];
end
endfunction

function automatic stream1(input [5:0] base);
begin
    stream1 = flip_x ? stage_data[31 - base] : stage_data[base];
end
endfunction

reg [4:0] palette;

assign vram_addr = ( state < APPLY_SCROLL ) ? scroll_addr : { vram_row_addr, tile_addr };

assign color_out = { pal_buffer[pixel_out_idx[4:0]], buffer[pixel_out_idx[4:0]] };

reg prev_scan_active;

always_ff @(posedge clk) begin
    if (start_read) begin
        state <= READ_SCROLL0;
    end

    if (load_buffer) begin
        case(load_slot)
            0: begin
                buffer[0] <= stream5(0); pal_buffer[0] <= palette;
                buffer[1] <= stream5(5); pal_buffer[1] <= palette;
                buffer[2] <= stream5(10); pal_buffer[2] <= palette;
                buffer[3] <= stream5(15); pal_buffer[3] <= palette;
                buffer[4] <= stream5(20); pal_buffer[4] <= palette;
                buffer[5] <= stream5(25); pal_buffer[5] <= palette;
                if (flip_x)
                    buffer[6][4:3] <= stream2(30);
                else
                    buffer[6][1:0] <= stream2(30);
            end
            1: begin
                if (flip_x)
                    buffer[6][2:0] <= stream3(0);
                else
                    buffer[6][4:2] <= stream3(0);
                pal_buffer[6] <= palette;

                buffer[7] <= stream5(3); pal_buffer[7] <= palette;
                buffer[8] <= stream5(8); pal_buffer[8] <= palette;
                buffer[9] <= stream5(13); pal_buffer[9] <= palette;
                buffer[10] <= stream5(18); pal_buffer[10] <= palette;
                buffer[11] <= stream5(23); pal_buffer[11] <= palette;

                if (flip_x)
                    buffer[12][4:1] <= stream4(28);
                else
                    buffer[12][3:0] <= stream4(28);
            end
            2: begin
                if (flip_x)
                    buffer[12][0] <= stream1(0);
                else
                    buffer[12][4] <= stream1(0);
                pal_buffer[12] <= palette;

                buffer[13] <= stream5(1); pal_buffer[13] <= palette;
                buffer[14] <= stream5(6); pal_buffer[14] <= palette;
                buffer[15] <= stream5(11); pal_buffer[15] <= palette;
                buffer[16] <= stream5(16); pal_buffer[16] <= palette;
                buffer[17] <= stream5(21); pal_buffer[17] <= palette;
                buffer[18] <= stream5(26); pal_buffer[18] <= palette;

                if (flip_x)
                    buffer[19][4] <= stream1(31);
                else
                    buffer[19][0] <= stream1(31);
            end
            3: begin
                if (flip_x)
                    buffer[19][3:0] <= stream4(0);
                else
                    buffer[19][4:1] <= stream4(0);
                pal_buffer[19] <= palette;

                buffer[20] <= stream5(4); pal_buffer[20] <= palette;
                buffer[21] <= stream5(9); pal_buffer[21] <= palette;
                buffer[22] <= stream5(14); pal_buffer[22] <= palette;
                buffer[23] <= stream5(19); pal_buffer[23] <= palette;
                buffer[24] <= stream5(24); pal_buffer[24] <= palette;

                if (flip_x)
                    buffer[25][4:2] <= stream3(29);
                else
                    buffer[25][2:0] <= stream3(29);
            end
            4: begin
                if (flip_x)
                    buffer[25][1:0] <= stream2(0);
                else
                    buffer[25][4:3] <= stream2(0);
                pal_buffer[25] <= palette;

                buffer[26] <= stream5(2); pal_buffer[26] <= palette;
                buffer[27] <= stream5(7); pal_buffer[27] <= palette;
                buffer[28] <= stream5(12); pal_buffer[28] <= palette;
                buffer[29] <= stream5(17); pal_buffer[29] <= palette;
                buffer[30] <= stream5(22); pal_buffer[30] <= palette;
                buffer[31] <= stream5(27); pal_buffer[31] <= palette;
            end
            default: begin end
        endcase
        
        load_buffer <= 0;
        pixel_in_idx <= pixel_in_idx + slot_increment[load_slot];
        load_slot <= load_slot + 1;
        if (load_slot == 4) load_slot <= 0;
    end

    if (scale_shifter_x[0]) begin
        pixel_out_idx <= pixel_out_idx + 1;
        scale_shifter_x <= { scale_shifter_x[0], scale_shifter_x[31:1] };
    end

    if (ce_pixel) begin
        if (scan_active) begin
            pixel_out_idx <= pixel_out_idx + 1;
            scale_shifter_x <= { scale_shifter_x[0], scale_shifter_x[31:1] };
        end

        case(state)
            READ_SCROLL0: begin
                state <= READ_SCROLL1;
                scroll_addr <= 15'h7000 + { 6'b0, screen_y[7:0], 1'b0 };
            end

            READ_SCROLL1: begin
                scroll[7:0] <= vram_din;
                state <= READ_SCROLL2;
                scroll_addr <= 15'h7000 + { 6'b0, screen_y[7:0], 1'b1 };
            end

            READ_SCROLL2: begin
                scroll[15:8] <= vram_din;
                state <= APPLY_SCROLL;
            end

            APPLY_SCROLL: begin
                pixel_out_idx <= { 4'd1, scrolled_x[4:0] };
                scale_shifter_x <= 0; //scale_bits_x;
                pixel_in_idx <= 0;
                vram_row_addr <= { 1'b0, y[10:5] };
                tile_addr <= {scrolled_x[10:5], 2'b00};
                state <= READ0;
            end

            READ0: begin
                state <= READ1;
            end
            READ1: begin
                tile_code[7:0] <= vram_din;
                tile_addr <= tile_addr + 1;
                state <= READ2;
            end
            READ2: begin
                tile_code[15:8] <= vram_din;
                tile_addr <= tile_addr + 1;
                state <= READ3;
            end
            READ3: begin
                tile_attrib[7:0] <= vram_din;
                tile_addr <= tile_addr + 2;
                state <= ROM_REQ0;
            end

            READ4: state <= READ5;
            READ5: state <= READ6;
            READ6: state <= ROM_REQ0;
 
            ROM_REQ0: begin
                rom_address <= { tile_code[14:0], flip_y ? ~y[4:0] : y[4:0], 4'd0 }
                             + { 2'b0, tile_code[14:0], flip_y ? ~y[4:0] : y[4:0], 2'd0 }
                             + (flip_x ? 16 : 0);
                rom_req <= ~rom_req;
                palette <= tile_attrib[5:1];
                state <= ROM_WAIT0;
            end

            ROM_WAIT0: begin
                if (rom_req == rom_ack && buffer_ready) begin
                    stage_data <= rom_data;
                    load_buffer <= 1;
                    rom_address <= flip_x ? rom_address - 4 : rom_address + 4;
                    rom_req <= ~rom_req;
                    state <= ROM_WAIT1;
                end
            end

            ROM_WAIT1: begin
                if (rom_req == rom_ack && buffer_ready) begin
                    stage_data <= rom_data;
                    load_buffer <= 1;
                    rom_address <= flip_x ? rom_address - 4 : rom_address + 4;
                    rom_req <= ~rom_req;
                    state <= ROM_WAIT2;
                end
            end

            ROM_WAIT2: begin
                if (rom_req == rom_ack && buffer_ready) begin
                    stage_data <= rom_data;
                    load_buffer <= 1;
                    rom_address <= flip_x ? rom_address - 4 : rom_address + 4;
                    rom_req <= ~rom_req;
                    state <= ROM_WAIT3;
                end
            end

            ROM_WAIT3: begin
                if (rom_req == rom_ack && buffer_ready) begin
                    stage_data <= rom_data;
                    load_buffer <= 1;
                    rom_address <= flip_x ? rom_address - 4 : rom_address + 4;
                    rom_req <= ~rom_req;
                    state <= ROM_WAIT4;
                end
            end

            ROM_WAIT4: begin
                if (rom_req == rom_ack && buffer_ready) begin
                    stage_data <= rom_data;
                    load_buffer <= 1;
                    state <= READ0;
                end
            end

            DONE: begin rom_req <= rom_ack; end
            default: begin end
        endcase
    end

    prev_scan_active <= scan_active;
    if (prev_scan_active & ~scan_active) begin
        load_slot <= 0;
        load_buffer <= 0;
        state <= DONE;
    end

end

endmodule
