wickerwaka/Arcade-IGSPGM_MiSTer/testroms/pgm_bios_z80_data.h

#if !defined(PGM_BIOS_Z80_DATA_H)
#define PGM_BIOS_Z80_DATA_H 1

#include "system.h"

/* Extracted from ~/Source/PGM-BIOS/pgm_p02s_raw_initialized_globals.c. */
static const u8 embedded_z80_sound_driver_blob[13542] = {
    0xed, 0x56, 0xc3, 0x00, 0x01, 0x00, 0x00, 0x00, 0x00, 0x00, 0x00, 0x00,
    0x00, 0x00, 0x00, 0x00, 0x00, 0x00, 0x00, 0x00, 0x00, 0x00, 0x00, 0x00,
    0x00, 0x00, 0x00, 0x00, 0x00, 0x00, 0x00, 0x00, 0x00, 0x00, 0x00, 0x00,
    0x00, 0x00, 0x00, 0x00, 0x00, 0x00, 0x00, 0x00, 0x00, 0x00, 0x00, 0x00,
    0x00, 0x00, 0x00, 0x00, 0x00, 0x00, 0x00, 0x00, 0xc3, 0x0b, 0x01, 0x00,
    0x00, 0x00, 0x00, 0x00, 0x00, 0x50, 0x00, 0x00, 0x00, 0x00, 0x00, 0x00,
    0x00, 0x00, 0x00, 0x00, 0x00, 0x00, 0x00, 0x00, 0x70, 0x00, 0x00, 0x00,
    0x00, 0x00, 0x00, 0x00, 0x00, 0x00, 0x00, 0x00, 0x00, 0x00, 0x00, 0x00,
    0x00, 0x40, 0x00, 0x4a, 0x00, 0x00, 0xc3, 0x28, 0x01, 0x00, 0x00, 0x00,
    0x00, 0x00, 0x00, 0x00, 0x00, 0x00, 0x00, 0x00, 0x00, 0x00, 0x00, 0x00,
    0x00, 0x00, 0x00, 0x00, 0x00, 0x00, 0x00, 0x00, 0x00, 0x00, 0x00, 0x00,
    0x00, 0x00, 0x00, 0x00, 0x00, 0x00, 0x00, 0x00, 0x00, 0x00, 0x00, 0x00,
    0x00, 0x00, 0x00, 0x00, 0x00, 0x00, 0x00, 0x00, 0x00, 0x00, 0x00, 0x00,
    0x00, 0x00, 0x00, 0x00, 0x00, 0x00, 0x00, 0x00, 0x00, 0x00, 0x00, 0x00,
    0x00, 0x00, 0x00, 0x00, 0x00, 0x00, 0x00, 0x00, 0x00, 0x00, 0x00, 0x00,
    0x00, 0x00, 0x00, 0x00, 0x00, 0x00, 0x00, 0x00, 0x00, 0x00, 0x00, 0x00,
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
    0x40, 0x00, 0x11, 0x2b, 0x00, 0x80, 0x14, 0xbd, 0x00, 0x70, 0xcc, 0xbd,
    0x40, 0x00, 0x11, 0x2b, 0x00, 0x80, 0xcc, 0xbd, 0x00, 0xd0, 0x95, 0xbe,
    0x40, 0x00, 0x11, 0x2b, 0x00, 0xe0, 0x95, 0xbe
};

#endif /* PGM_BIOS_Z80_DATA_H */
