wickerwaka/Arcade-IGSPGM_MiSTer/rtl/sdram.sv

//
// sdram
// Copyright (c) 2015-2019 Sorgelig
//
// Some parts of SDRAM code used from project:
// http://hamsterworks.co.nz/mediawiki/index.php/Simple_SDRAM_Controller
//
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
module sdram
(
    input             init,        // reset to initialize RAM
    input             clk,         // clock 64MHz

    input             doRefresh,

    inout  reg [15:0] SDRAM_DQ,    // 16 bit bidirectional data bus
    output reg [12:0] SDRAM_A,     // 13 bit multiplexed address bus
    output            SDRAM_DQML,  // two byte masks
    output            SDRAM_DQMH,  //
    output reg  [1:0] SDRAM_BA,    // two banks
    output            SDRAM_nCS,   // a single chip select
    output            SDRAM_nWE,   // write enable
    output            SDRAM_nRAS,  // row address select
    output            SDRAM_nCAS,  // columns address select
    output            SDRAM_CKE,   // clock enable
    output            SDRAM_CLK,   // clock for chip

    input      [26:0] ch1_addr,    // 25 bit address for 8bit mode. addr[0] = 0 for 16bit mode for correct operations.
    output reg [31:0] ch1_dout,    // data output to cpu
    input             ch1_req,     // request
    output reg        ch1_ack,

    input      [26:0] ch2_addr,
    output reg [63:0] ch2_dout,
    input             ch2_req,
    output reg        ch2_ack,

    input      [26:0] ch3_addr,
    output reg [63:0] ch3_dout,
    input      [15:0] ch3_din,
    input      [ 1:0] ch3_be,
    input             ch3_req,
    input             ch3_rnw,     // 1 - read, 0 - write
    output reg        ch3_ack,

    input      [26:0] ch4_addr,
    output reg [63:0] ch4_dout,
    input             ch4_req,
    output reg        ch4_ack
);

assign SDRAM_nCS  = chip;
assign SDRAM_nRAS = command[2];
assign SDRAM_nCAS = command[1];
assign SDRAM_nWE  = command[0];
assign SDRAM_CKE  = 1;
assign {SDRAM_DQMH,SDRAM_DQML} = SDRAM_A[12:11];


// Burst length = 4
localparam BURST_LENGTH        = 4;
localparam BURST_CODE          = (BURST_LENGTH == 8) ? 3'b011 : (BURST_LENGTH == 4) ? 3'b010 : (BURST_LENGTH == 2) ? 3'b001 : 3'b000;  // 000=1, 001=2, 010=4, 011=8
localparam ACCESS_TYPE         = 1'b0;     // 0=sequential, 1=interleaved
localparam CAS_LATENCY         = 3'd3;     // 2 for < 100MHz, 3 for >100MHz
localparam OP_MODE             = 2'b00;    // only 00 (standard operation) allowed
localparam NO_WRITE_BURST      = 1'b1;     // 0= write burst enabled, 1=only single access write
localparam MODE                = {3'b000, NO_WRITE_BURST, OP_MODE, CAS_LATENCY, ACCESS_TYPE, BURST_CODE};

localparam sdram_startup_cycles= 14'd12100;// 100us, plus a little more, @ 100MHz
localparam cycles_per_refresh  = 14'd500;  // (64000*64)/8192-1 Calc'd as (64ms @ 64MHz)/8192 rose
localparam startup_refresh_max = 14'b11111111111111;

// SDRAM commands
wire [2:0] CMD_NOP             = 3'b111;
wire [2:0] CMD_ACTIVE          = 3'b011;
wire [2:0] CMD_READ            = 3'b101;
wire [2:0] CMD_WRITE           = 3'b100;
wire [2:0] CMD_PRECHARGE       = 3'b010;
wire [2:0] CMD_AUTO_REFRESH    = 3'b001;
wire [2:0] CMD_LOAD_MODE       = 3'b000;

reg [13:0] refresh_count = startup_refresh_max - sdram_startup_cycles;
reg  [2:0] command;
reg        chip;

localparam STATE_STARTUP = 0;
localparam STATE_WAIT    = 1;
localparam STATE_RW1     = 2;
localparam STATE_IDLE    = 4;
localparam STATE_IDLE_1  = 5;
localparam STATE_IDLE_2  = 6;
localparam STATE_IDLE_3  = 7;
localparam STATE_IDLE_4  = 8;
localparam STATE_IDLE_5  = 9;
localparam STATE_RFSH    = 10;


always @(posedge clk) begin
    reg [CAS_LATENCY+BURST_LENGTH+1:0] data_ready_delay1, data_ready_delay2, data_ready_delay3, data_ready_delay4;

    reg        saved_wr;
    reg [12:0] cas_addr;
    reg [15:0] saved_data;
    reg [15:0] dq_reg;
    reg  [3:0] state = STATE_STARTUP;

    reg       ch1_req_1, ch2_req_1, ch3_req_1, ch4_req_1;
    reg       ch1_rq, ch2_rq, ch3_rq, ch4_rq;
    reg [1:0] ch;

    reg [26:1] ch1_addr_1, ch2_addr_1, ch3_addr_1, ch4_addr_1;

    reg        ch3_rnw_1;
    reg [15:0] ch3_din_1;
    reg [ 1:0] ch3_be_1;

    reg        doRefresh_1;

    ch1_req_1 <= ch1_req;
    ch2_req_1 <= ch2_req;
    ch3_req_1 <= ch3_req;
    ch4_req_1 <= ch4_req;

    ch3_rnw_1  <= ch3_rnw;
    ch3_addr_1 <= ch3_addr[26:1];
    ch3_din_1  <= ch3_din;
    ch3_be_1   <= ch3_be;

    ch1_addr_1 <= ch1_addr[26:1];
    ch2_addr_1 <= ch2_addr[26:1];
    ch4_addr_1 <= ch4_addr[26:1];

    doRefresh_1 <= doRefresh;

    if (ch1_req != ch1_req_1) ch1_rq <= 1;
    if (ch2_req != ch2_req_1) ch2_rq <= 1;
    if (ch3_req != ch3_req_1) ch3_rq <= 1;
    if (ch4_req != ch4_req_1) ch4_rq <= 1;

    refresh_count <= refresh_count+1'b1;

    data_ready_delay1 <= data_ready_delay1>>1;
    data_ready_delay2 <= data_ready_delay2>>1;
    data_ready_delay3 <= data_ready_delay3>>1;
    data_ready_delay4 <= data_ready_delay4>>1;

    dq_reg <= SDRAM_DQ;

    if(data_ready_delay1[4]) ch1_dout[15:00] <= dq_reg;
    if(data_ready_delay1[3]) ch1_dout[31:16] <= dq_reg;
    if(data_ready_delay1[3]) ch1_ack <= ch1_req;

    if(data_ready_delay2[4]) ch2_dout[15:00] <= dq_reg;
    if(data_ready_delay2[3]) ch2_dout[31:16] <= dq_reg;
    if(data_ready_delay2[2]) ch2_dout[47:32] <= dq_reg;
    if(data_ready_delay2[1]) ch2_dout[63:48] <= dq_reg;
    if(data_ready_delay2[1]) ch2_ack <= ch2_req;

    if(data_ready_delay3[4]) ch3_dout[15:00] <= dq_reg;
    if(data_ready_delay3[3]) ch3_dout[31:16] <= dq_reg;
    if(data_ready_delay3[2]) ch3_dout[47:32] <= dq_reg;
    if(data_ready_delay3[1]) ch3_dout[63:48] <= dq_reg;
    if(data_ready_delay3[1]) ch3_ack <= ch3_req;

    if(data_ready_delay4[4]) ch4_dout[15:00] <= dq_reg;
    if(data_ready_delay4[3]) ch4_dout[31:16] <= dq_reg;
    if(data_ready_delay4[2]) ch4_dout[47:32] <= dq_reg;
    if(data_ready_delay4[1]) ch4_dout[63:48] <= dq_reg;
    if(data_ready_delay4[1]) ch4_ack <= ch4_req;

    SDRAM_DQ <= 16'bZ;

    command <= CMD_NOP;
    case (state)
        STATE_STARTUP: begin
            SDRAM_A    <= 0;
            SDRAM_BA   <= 0;

            if (refresh_count == (startup_refresh_max-64)) chip <= 0;
            if (refresh_count == (startup_refresh_max-32)) chip <= 1;

            // All the commands during the startup are NOPS, except these
            if (refresh_count == startup_refresh_max-63 || refresh_count == startup_refresh_max-31) begin
                // ensure all rows are closed
                command     <= CMD_PRECHARGE;
                SDRAM_A[10] <= 1;  // all banks
                SDRAM_BA    <= 2'b00;
            end
            if (refresh_count == startup_refresh_max-55 || refresh_count == startup_refresh_max-23) begin
                // these refreshes need to be at least tREF (66ns) apart
                command     <= CMD_AUTO_REFRESH;
            end
            if (refresh_count == startup_refresh_max-47 || refresh_count == startup_refresh_max-15) begin
                command     <= CMD_AUTO_REFRESH;
            end
            if (refresh_count == startup_refresh_max-39 || refresh_count == startup_refresh_max-7) begin
                // Now load the mode register
                command     <= CMD_LOAD_MODE;
                SDRAM_A     <= MODE;
            end

            if (!refresh_count) begin
                state   <= STATE_IDLE;
                refresh_count <= 0;
            end
        end

        STATE_IDLE_5: state <= STATE_IDLE_4;
        STATE_IDLE_4: state <= STATE_IDLE_3;
        STATE_IDLE_3: state <= STATE_IDLE_2;
        STATE_IDLE_2: state <= STATE_IDLE_1;
        STATE_IDLE_1: state <= STATE_IDLE;

        STATE_RFSH: begin
            state    <= STATE_IDLE_5;
            command  <= CMD_AUTO_REFRESH;
            chip     <= 1;
        end

        STATE_IDLE: begin
            if (refresh_count > cycles_per_refresh) begin // emergency refresh, mainly for downloading rom/paused core
                state         <= STATE_RFSH;
                command       <= CMD_AUTO_REFRESH;
                refresh_count <= refresh_count - cycles_per_refresh + 1'd1;
                chip          <= 0;
            end
            else if(ch2_rq) begin
                {cas_addr[12:9],SDRAM_BA,SDRAM_A,cas_addr[8:0]} <= {2'b00, 1'b1, ch2_addr_1[25:1]};
                chip       <= ch2_addr_1[26];
                saved_wr   <= 0;
                ch         <= 1;
                ch2_rq     <= 0;
                command    <= CMD_ACTIVE;
                state      <= STATE_WAIT;
            end
            else if(ch1_rq) begin
                {cas_addr[12:9],SDRAM_BA,SDRAM_A,cas_addr[8:0]} <= {2'b00, 1'b1, ch1_addr_1[25:1]};
                chip       <= ch1_addr_1[26];
                saved_wr   <= 0;
                ch         <= 0;
                ch1_rq     <= 0;
                command    <= CMD_ACTIVE;
                state      <= STATE_WAIT;
            end
            else if(ch4_rq) begin
                {cas_addr[12:9],SDRAM_BA,SDRAM_A,cas_addr[8:0]} <= {2'b00, 1'b1, ch4_addr_1[25:1]};
                chip       <= ch4_addr_1[26];
                saved_wr   <= 0;
                ch         <= 3;
                ch4_rq     <= 0;
                command    <= CMD_ACTIVE;
                state      <= STATE_WAIT;
            end
            else if(ch3_rq) begin
                chip       <= ch3_addr_1[26];
                saved_data <= ch3_din_1;
                saved_wr   <= ~ch3_rnw_1;
                ch         <= 2;
                ch3_rq     <= 0;
                if (ch3_rnw_1)
                    {cas_addr[12:9],SDRAM_BA,SDRAM_A,cas_addr[8:0]} <= {2'b00, 1'b1, ch3_addr_1[25:1]};
                else
                    {cas_addr[12:9],SDRAM_BA,SDRAM_A,cas_addr[8:0]} <= {~ch3_be_1, 1'b1, ch3_addr_1[25:1]};
                command    <= CMD_ACTIVE;
                state      <= STATE_WAIT;
            end
            else if (doRefresh_1) begin
                state         <= STATE_RFSH;
                command       <= CMD_AUTO_REFRESH;
                refresh_count <= 0;
                chip          <= 0;
            end
        end

        STATE_WAIT: state <= STATE_RW1;
        STATE_RW1: begin
            SDRAM_A <= cas_addr;
            if(saved_wr) begin
                command  <= CMD_WRITE;
                SDRAM_DQ <= saved_data;
                if(ch == 0) ch1_ack  <= ch1_req;
                if(ch == 1) ch2_ack  <= ch2_req;
                if(ch == 2) ch3_ack  <= ch3_req;
                if(ch == 3) ch4_ack  <= ch4_req;
                state <= STATE_IDLE_2;
            end
            else begin
                command <= CMD_READ;
                state   <= STATE_IDLE_5;
                     if(ch == 0) data_ready_delay1[CAS_LATENCY+BURST_LENGTH+1] <= 1;
                else if(ch == 1) data_ready_delay2[CAS_LATENCY+BURST_LENGTH+1] <= 1;
                else if(ch == 2) data_ready_delay3[CAS_LATENCY+BURST_LENGTH+1] <= 1;
                else             data_ready_delay4[CAS_LATENCY+BURST_LENGTH+1] <= 1;
            end
        end

    endcase

    if (init) begin
        state <= STATE_STARTUP;
        refresh_count <= startup_refresh_max - sdram_startup_cycles;
    end
end

altddio_out
#(
    .extend_oe_disable("OFF"),
    .intended_device_family("Cyclone V"),
    .invert_output("OFF"),
    .lpm_hint("UNUSED"),
    .lpm_type("altddio_out"),
    .oe_reg("UNREGISTERED"),
    .power_up_high("OFF"),
    .width(1)
)
sdramclk_ddr
(
    .datain_h(1'b0),
    .datain_l(1'b1),
    .outclock(clk),
    .dataout(SDRAM_CLK),
    .aclr(1'b0),
    .aset(1'b0),
    .oe(1'b1),
    .outclocken(1'b1),
    .sclr(1'b0),
    .sset(1'b0)
);

endmodule
