wickerwaka/Arcade-IGSPGM_MiSTer/rtl/fx68k/hdl/verilator/fx68k.sv

//
// FX68K
//
// M68000 cycle accurate, fully synchronous
// Copyright (c) 2018,2021 by Jorge Cwik
//
// TODO:
// - Everything except bus retry already implemented.

`timescale 1 ns / 1 ns

//`define USE_E_CLKEN
/*
	Define USE_E_CLKEN will output two signals that generate a single cycle pulse just before the raising and falling edges of E.
	Use this when you need to generate changes that must be simultaneous with these edges.
	Most systems don't need this. Note that these signals are not registered.
 */

// Define this to run a self contained compilation test build
// `define FX68K_TEST

localparam CF = 0, VF = 1, ZF = 2, NF = 3, XF = 4, SF = 13;

localparam UADDR_WIDTH = 10;
localparam UROM_WIDTH  = 17;
localparam UROM_DEPTH  = 1024;

localparam NADDR_WIDTH = 9;
localparam NANO_WIDTH  = 68;
localparam NANO_DEPTH  = 336;

localparam BSER1_NMA = 2'b11;
localparam RSTP0_NMA = 2'b10;
localparam HALT1_NMA = 2'b01;
localparam TRAC1_NMA = 9'd448;
localparam ITLX1_NMA = 9'd452;

localparam TVN_SPURIOUS = 4'd12;
localparam TVN_AUTOVEC = 4'd13;
localparam TVN_INTERRUPT = 4'd15;

localparam NANO_DOB_DBD = 2'b01;
localparam NANO_DOB_ADB = 2'b10;
localparam NANO_DOB_ALU = 2'b11;

module fx68k(
	input clk,
	input HALTn,					// Used for single step only. Force high if not used
	// input logic HALTn = 1'b1,			// Not all tools support default port values

	// These two signals don't need to be registered. They are not async reset.
	input extReset,			// External sync reset on emulated system
	input pwrUp,			// Asserted together with reset on emulated system coldstart
	input enPhi1, enPhi2,	// Clock enables. Next cycle is PHI1 or PHI2

	output eRWn, output ASn, output LDSn, output UDSn,
	output logic E, output VMAn,

`ifdef USE_E_CLKEN
	// Next cycle would be raising/falling edge of E output
	output E_PosClkEn, E_NegClkEn,
`endif

	output FC0, output FC1, output FC2,
	output BGn,
	output oRESETn, output oHALTEDn,
	input DTACKn, input VPAn,
	input BERRn,
	input BRn, BGACKn,
	input IPL0n, input IPL1n, input IPL2n,
	input [15:0] iEdb, output [15:0] oEdb,
	output [23:1] eab
	);
	// CPU registers
	wire [31:0] PC, D0,D1,D2,D3,D4,D5,D6,D7, A0,A1,A2,A3,A4,A5,A6,A7;


	// extReset: 		External sync reset on emulated system
	// pwrUp:	 		Asserted together with reset on emulated system coldstart
	// enPhi1, enPhi2:	Clock enables. Next cycle is PHI1 or PHI2

	wire Clks_clk, Clks_extReset, Clks_pwrUp, Clks_enPhi1, Clks_enPhi2;

	assign Clks_clk = clk;
	assign Clks_extReset = extReset;
	assign Clks_pwrUp = pwrUp;
	assign Clks_enPhi1 = enPhi1;
	assign Clks_enPhi2 = enPhi2;

	wire wClk;

	wire Irdecod_isPcRel, Irdecod_isTas, Irdecod_implicitSp, Irdecod_toCcr;
	wire Irdecod_rxIsDt, Irdecod_ryIsDt, Irdecod_rxIsUsp, Irdecod_rxIsMovem, Irdecod_movemPreDecr;
	wire Irdecod_isByte, Irdecod_isMovep, Irdecod_inhibitCcr, Irdecod_rxIsAreg, Irdecod_ryIsAreg;
	wire [2:0] Irdecod_rx;
	wire [2:0] Irdecod_ry;
	wire [15:0] Irdecod_ftuConst;
	wire [5:0] Irdecod_macroTvn;

	// wire Nanod_adb2Dob, Nanod_dbd2Dob, Nanod_alu2Dob;
	wire Nanod_permStart, Nanod_waitBusFinish, Nanod_isWrite, Nanod_busByte, Nanod_isRmc, Nanod_noLowByte;
	wire Nanod_noHighByte, Nanod_updTpend, Nanod_clrTpend, Nanod_tvn2Ftu, Nanod_const2Ftu, Nanod_ftu2Dbl;
	wire Nanod_ftu2Abl, Nanod_abl2Pren, Nanod_updPren, Nanod_inl2psw, Nanod_ftu2Sr, Nanod_sr2Ftu, Nanod_ftu2Ccr;
	wire Nanod_pswIToFtu, Nanod_initST, Nanod_ird2Ftu, Nanod_ssw2Ftu, Nanod_Ir2Ird, Nanod_auClkEn, Nanod_noSpAlign;
	wire Nanod_todbin, Nanod_toIrc, Nanod_abh2Ath, Nanod_dbh2Ath, Nanod_ath2Dbh, Nanod_ath2Abh, Nanod_dbl2Atl;
	wire Nanod_db2Aob, Nanod_ab2Aob, Nanod_au2Aob, Nanod_aob2Ab, Nanod_updSsw, Nanod_abh2reg, Nanod_abl2reg;
	wire Nanod_reg2abl, Nanod_reg2abh, Nanod_dbh2reg, Nanod_dbl2reg, Nanod_reg2dbl, Nanod_reg2dbh, Nanod_ryh2dbh;
	wire Nanod_atl2Abl, Nanod_abl2Atl, Nanod_atl2Dbl, Nanod_ssp, Nanod_rxlDbl, Nanod_aluFinish, Nanod_ryl2ab;
	wire Nanod_pchdbh, Nanod_pcldbl, Nanod_pclabl, Nanod_pchabh, Nanod_rz, Nanod_aluActrl, Nanod_aluInit;
	wire Nanod_au2Db, Nanod_au2Ab, Nanod_au2Pc, Nanod_dbin2Abd, Nanod_dbin2Dbd, Nanod_abdIsByte, Nanod_ablAbd;
	wire Nanod_rxh2dbh, Nanod_rxh2abh, Nanod_dbl2rxl, Nanod_abh2rxh, Nanod_dbh2rxh, Nanod_extDbh, Nanod_extAbh;
	wire Nanod_ablAbh, Nanod_dblDbd, Nanod_dblDbh, Nanod_alu2Dbd, Nanod_alu2Abd, Nanod_abd2Dcr, Nanod_ryh2abh;
	wire Nanod_dbd2Alue, Nanod_alue2Dbd, Nanod_dcr2Dbd, Nanod_dbd2Alub, Nanod_abd2Alub, Nanod_ryl2db;
	wire Nanod_rxl2db, Nanod_rxl2ab, Nanod_abl2rxl, Nanod_dbh2ryh, Nanod_abh2ryh, Nanod_dbl2ryl, Nanod_abl2ryl;
	wire [2:0] Nanod_auCntrl;
	wire [1:0] Nanod_dobCtrl;
	wire [2:0] Nanod_aluColumn;
	wire [1:0] Nanod_aluDctrl;

	// Internal sub clocks T1-T4
	enum int unsigned { T0 = 0, T1, T2, T3, T4} tState;
	wire enT1 = Clks_enPhi1 & (tState == T4) & ~wClk;
	wire enT2 = Clks_enPhi2 & (tState == T1);
	wire enT3 = Clks_enPhi1 & (tState == T2);
	wire enT4 = Clks_enPhi2 & ((tState == T0) | (tState == T3));

	// T4 continues ticking during reset and group0 exception.
	// We also need it to erase ucode output latched on T4.
	always @( posedge Clks_clk) begin
		if( Clks_pwrUp)
			tState <= T0;
		else begin
		case( tState)
		T0: if( Clks_enPhi2) tState <= T4;
		T1: if( Clks_enPhi2) tState <= T2;
		T2: if( Clks_enPhi1) tState <= T3;
		T3: if( Clks_enPhi2) tState <= T4;
		T4: if( Clks_enPhi1) tState <= wClk ? T0 : T1;
		endcase
		end
	end

	// The following signals are synchronized with 3 couplers, phi1-phi2-phi1.
	// Will be valid internally one cycle later if changed at the rasing edge of the clock.
	//
	// DTACK, BERR

	// DTACK valid at S6 if changed at the rasing edge of S4 to avoid wait states.
	// SNC (sncClkEn) is deasserted together (unless DTACK asserted too early).
	//
	// We synchronize some signals half clock earlier. We compensate later
	reg rDtack, rBerr;
	reg [2:0] rIpl, iIpl;
	reg Vpai, BeI, Halti, BRi, BgackI, BeiDelay;
	// reg rBR, rHALT;
	wire BeDebounced = ~( BeI | BeiDelay);

	always @( posedge Clks_clk) begin
		if( Clks_pwrUp) begin
			rBerr <= 1'b0;
			BeI <= 1'b0;
		end
		else if( Clks_enPhi2) begin
			rDtack <= DTACKn;
			rBerr <= BERRn;
			rIpl <= ~{ IPL2n, IPL1n, IPL0n};
			iIpl <= rIpl;

			// Needed for cycle accuracy but only if BR or HALT are asserted on the wrong edge of the clock
			// rBR <= BRn;
			// rHALT <= HALTn;
		end
		else if( Clks_enPhi1) begin
			Vpai <= VPAn;
			BeI <= rBerr;
			BeiDelay <= BeI;
			BgackI <= BGACKn;

			BRi <= BRn;
			Halti <= HALTn;
			// BRi <= rBR;
			// Halti <= rHALT;
		end
	end

	// Instantiate micro and nano rom
	logic [NANO_WIDTH-1:0] nanoLatch;
	logic [NANO_WIDTH-1:0] nanoOutput;
	logic [UROM_WIDTH-1:0] microLatch;
	logic [UROM_WIDTH-1:0] microOutput;

	logic [UADDR_WIDTH-1:0] microAddr, nma;
	logic [NADDR_WIDTH-1:0] nanoAddr, orgAddr;
	wire rstUrom;

	// For the time being, address translation is done for nanorom only.
	microToNanoAddr microToNanoAddr( .uAddr( nma), .orgAddr);

	// Output of these modules will be updated at T2 at the latest (depending on clock division)

	nanoRom nanoRom( .clk( Clks_clk), .nanoAddr, .nanoOutput);
	uRom uRom( .clk( Clks_clk), .microAddr, .microOutput);

	always @( posedge Clks_clk) begin
		// uaddr originally latched on T1, except bits 6 & 7, the conditional bits, on T2
		// Seems we can latch whole address at either T1 or T2

		// Originally it's invalid on hardware reset, and forced later when coming out of reset
		if( Clks_pwrUp) begin
			microAddr <= {8'b0, RSTP0_NMA};
			nanoAddr <= {7'b0, RSTP0_NMA};
		end
		else if( enT1) begin
			microAddr <= nma;
			nanoAddr <= orgAddr;				// Register translated uaddr to naddr
		end

		if( Clks_extReset) begin
			microLatch <= '0;
			nanoLatch <= '0;
		end
		else if( rstUrom) begin
			// Originally reset these bits only. Not strictly needed like this.
			// Can reset the whole register if it is important.
			{ microLatch[16], microLatch[15], microLatch[0]} <= '0;
			nanoLatch <= '0;
		end
		else if( enT3) begin
			microLatch <= microOutput;
			nanoLatch <= nanoOutput;
		end

	end

	reg Tpend;
	reg intPend;											// Interrupt pending
	reg pswT, pswS;
	reg [ 2:0] pswI;
	wire [7:0] ccr;

	wire [15:0] psw = { pswT, 1'b0, pswS, 2'b00, pswI, ccr};

	reg [15:0] ftu;
	reg [15:0] Irc, Ir, Ird;

	wire [15:0] alue;
	wire [15:0] Abl;
	wire prenEmpty, au05z, dcr4, ze;

	wire [UADDR_WIDTH-1:0] a1, a2, a3;
	wire isPriv, isIllegal, isLineA, isLineF;


	// IR & IRD forwarding
	always @( posedge Clks_clk) begin
		if( enT1) begin
			if( Nanod_Ir2Ird)
				Ird <= Ir;
			else if(microLatch[0])		// prevented by IR => IRD !
				Ir <= Irc;
		end
	end

	wire [3:0] tvn;
	wire waitBusCycle, busStarting;
	wire BusRetry = 1'b0;
	wire busAddrErr;
	wire bciWrite;						// Last bus cycle was write
	wire bgBlock, busAvail;
	wire addrOe;

	wire busIsByte = Nanod_busByte & (Irdecod_isByte | Irdecod_isMovep);
	wire aob0;

	reg iStop;								// Internal signal for ending bus cycle
	reg A0Err;								// Force bus/address error ucode
	reg excRst;								// Signal reset exception to sequencer
	reg BerrA;
	reg Spuria, Avia;
	wire Iac;

	reg rAddrErr, iBusErr, Err6591;
	wire iAddrErr = rAddrErr & addrOe;		// To simulate async reset
	wire enErrClk;

	// Reset micro/nano latch after T4 of the current ublock.
	assign rstUrom = Clks_enPhi1 & enErrClk;

	uaddrDecode uaddrDecode( .opcode( Ir), .a1, .a2, .a3, .isPriv, .isIllegal, .isLineA, .isLineF, .lineBmap());

	sequencer sequencer( .Clks_clk, .Clks_extReset, .enT3, .microLatch, .Ird,
		.A0Err, .excRst, .BerrA, .busAddrErr, .Spuria, .Avia,
		.Tpend, .intPend, .isIllegal, .isPriv, .isLineA, .isLineF,
		.nma, .a1, .a2, .a3, .tvn,
		.psw, .prenEmpty, .au05z, .dcr4, .ze, .alue01( alue[1:0]), .i11( Irc[ 11]) );

	excUnit excUnit( .Clks_clk, .Clks_extReset, .Clks_pwrUp, .Clks_enPhi2, .enT1, .enT2, .enT3, .enT4,
		.Irdecod_implicitSp, .Irdecod_rxIsDt, .Irdecod_ryIsDt, .Irdecod_rxIsUsp, .Irdecod_rxIsMovem, .Irdecod_movemPreDecr, .Irdecod_isByte,
		.Irdecod_rx, .Irdecod_ry, .Irdecod_rxIsAreg, .Irdecod_ryIsAreg, .Nanod_busByte, .Nanod_noLowByte, .Nanod_noHighByte, .Nanod_ftu2Dbl,
		.Nanod_ftu2Abl, .Nanod_abl2Pren, .Nanod_updPren, .Nanod_ftu2Ccr, .Nanod_auCntrl, .Nanod_dobCtrl, .Nanod_aluColumn, .Nanod_aluDctrl,
		.Nanod_auClkEn, .Nanod_noSpAlign, .Nanod_todbin, .Nanod_toIrc, .Nanod_abh2Ath, .Nanod_dbh2Ath, .Nanod_ath2Dbh, .Nanod_ath2Abh,
		.Nanod_dbl2Atl, .Nanod_db2Aob, .Nanod_ab2Aob, .Nanod_au2Aob, .Nanod_aob2Ab, .Nanod_abh2reg, .Nanod_abl2reg, .Nanod_reg2abl, .Nanod_reg2abh,
		.Nanod_dbh2reg, .Nanod_dbl2reg, .Nanod_reg2dbl, .Nanod_reg2dbh, .Nanod_abl2Atl, .Nanod_atl2Abl, .Nanod_atl2Dbl, .Nanod_ssp, .Nanod_rxlDbl,
		.Nanod_rxh2dbh, .Nanod_rxh2abh, .Nanod_dbl2rxl, .Nanod_dbh2rxh, .Nanod_rxl2db, .Nanod_rxl2ab, .Nanod_abl2rxl, .Nanod_abh2rxh, .Nanod_dbh2ryh,
		.Nanod_abh2ryh, .Nanod_ryl2db, .Nanod_ryl2ab, .Nanod_ryh2dbh, .Nanod_ryh2abh, .Nanod_dbl2ryl, .Nanod_abl2ryl, .Nanod_pchdbh, .Nanod_pcldbl,
		.Nanod_pclabl, .Nanod_pchabh, .Nanod_rz, .Nanod_aluActrl, .Nanod_aluInit, .Nanod_aluFinish, .Nanod_abd2Dcr, .Nanod_dcr2Dbd, .Nanod_dbd2Alue,
		.Nanod_alue2Dbd, .Nanod_dbd2Alub, .Nanod_abd2Alub, .Nanod_alu2Dbd, .Nanod_alu2Abd, .Nanod_au2Db, .Nanod_au2Ab, .Nanod_au2Pc, .Nanod_dbin2Abd,
		.Nanod_dbin2Dbd, .Nanod_extDbh, .Nanod_ablAbd, .Nanod_ablAbh, .Nanod_extAbh, .Nanod_dblDbd, .Nanod_dblDbh, .Nanod_abdIsByte, .Ird, .ftu, .iEdb, .pswS,
		.prenEmpty, .au05z, .dcr4, .ze, .AblOut( Abl), .eab, .aob0, .Irc, .oEdb,
		.alue, .ccr, .PC, .D0, .D1, .D2, .D3, .D4, .D5, .D6, .D7, .A0, .A1, .A2, .A3, .A4, .A5, .A6, .A7);

	nDecoder3 nDecoder( .Clks_clk, .enT2, .enT4, .microLatch, .nanoLatch, .Irdecod_isPcRel, .Irdecod_isTas, .Nanod_permStart, .Nanod_waitBusFinish, .Nanod_isWrite,
		.Nanod_busByte, .Nanod_isRmc, .Nanod_noLowByte, .Nanod_noHighByte, .Nanod_updTpend, .Nanod_clrTpend, .Nanod_tvn2Ftu, .Nanod_const2Ftu, .Nanod_ftu2Dbl, .Nanod_ftu2Abl,
		.Nanod_abl2Pren, .Nanod_updPren, .Nanod_inl2psw, .Nanod_ftu2Sr, .Nanod_sr2Ftu, .Nanod_ftu2Ccr, .Nanod_pswIToFtu, .Nanod_initST, .Nanod_auCntrl, .Nanod_dobCtrl,
		.Nanod_aluColumn, .Nanod_aluDctrl, .Nanod_ird2Ftu, .Nanod_ssw2Ftu, .Nanod_Ir2Ird, .Nanod_auClkEn, .Nanod_noSpAlign, .Nanod_todbin, .Nanod_toIrc, .Nanod_abh2Ath,
		.Nanod_dbh2Ath, .Nanod_ath2Dbh, .Nanod_ath2Abh, .Nanod_dbl2Atl, .Nanod_db2Aob, .Nanod_ab2Aob, .Nanod_au2Aob, .Nanod_aob2Ab, .Nanod_updSsw, .Nanod_abh2reg, .Nanod_abl2reg,
		.Nanod_reg2abl, .Nanod_reg2abh, .Nanod_dbh2reg, .Nanod_dbl2reg, .Nanod_reg2dbl, .Nanod_reg2dbh, .Nanod_abl2Atl, .Nanod_atl2Abl, .Nanod_atl2Dbl, .Nanod_ssp, .Nanod_rxlDbl,
		.Nanod_rxh2dbh, .Nanod_rxh2abh, .Nanod_dbl2rxl, .Nanod_dbh2rxh, .Nanod_rxl2db, .Nanod_rxl2ab, .Nanod_abl2rxl, .Nanod_abh2rxh, .Nanod_dbh2ryh, .Nanod_abh2ryh, .Nanod_ryl2db,
		.Nanod_ryl2ab, .Nanod_ryh2dbh, .Nanod_ryh2abh, .Nanod_dbl2ryl, .Nanod_abl2ryl, .Nanod_pchdbh, .Nanod_pcldbl, .Nanod_pclabl, .Nanod_pchabh, .Nanod_rz, .Nanod_aluActrl,
		.Nanod_aluInit, .Nanod_aluFinish, .Nanod_abd2Dcr, .Nanod_dcr2Dbd, .Nanod_dbd2Alue, .Nanod_alue2Dbd, .Nanod_dbd2Alub, .Nanod_abd2Alub, .Nanod_alu2Dbd, .Nanod_alu2Abd,
		.Nanod_au2Db, .Nanod_au2Ab, .Nanod_au2Pc, .Nanod_dbin2Abd, .Nanod_dbin2Dbd, .Nanod_extDbh, .Nanod_extAbh, .Nanod_ablAbd, .Nanod_ablAbh, .Nanod_dblDbd, .Nanod_dblDbh,
		.Nanod_abdIsByte);

	irdDecode irdDecode( .ird( Ird), .Irdecod_isPcRel, .Irdecod_isTas, .Irdecod_implicitSp, .Irdecod_toCcr, .Irdecod_rxIsDt, .Irdecod_ryIsDt, .Irdecod_rxIsUsp,
		.Irdecod_rxIsMovem, .Irdecod_movemPreDecr, .Irdecod_isByte, .Irdecod_isMovep, .Irdecod_rx, .Irdecod_ry, .Irdecod_rxIsAreg, .Irdecod_ryIsAreg, .Irdecod_ftuConst,
		.Irdecod_macroTvn, .Irdecod_inhibitCcr);

	busControl busControl( .Clks_clk, .Clks_extReset, .Clks_pwrUp, .Clks_enPhi1, .Clks_enPhi2, .enT1, .enT4, .permStart( Nanod_permStart), .permStop( Nanod_waitBusFinish), .iStop,
		.aob0, .isWrite( Nanod_isWrite), .isRmc( Nanod_isRmc), .isByte( busIsByte), .busAvail,
		.bciWrite, .addrOe, .bgBlock, .waitBusCycle, .busStarting, .busAddrErr,
		.rDtack, .BeDebounced, .Vpai,
		.ASn, .LDSn, .UDSn, .eRWn);

	busArbiter busArbiter( .Clks_clk, .Clks_extReset, .Clks_enPhi1, .Clks_enPhi2, .BRi, .BgackI, .Halti, .bgBlock, .busAvail, .BGn);


	// Output reset & halt control
	wire [1:0] uFc = microLatch[ 16:15];
	logic oReset, oHalted;
	assign oRESETn = !oReset;
	assign oHALTEDn = !oHalted;

	// FC without permStart is special, either reset or halt
	always @( posedge Clks_clk) begin
		if( Clks_pwrUp) begin
			oReset <= 1'b0;
			oHalted <= 1'b0;
		end
		else if( enT1) begin
			oReset <= (uFc == 2'b01) & !Nanod_permStart;
			oHalted <= (uFc == 2'b10) & !Nanod_permStart;
		end
	end

	logic [2:0] rFC;
	assign { FC2, FC1, FC0} = rFC;					// ~rFC;
	assign Iac = {rFC == 3'b111};					// & Control output enable !!

	always @( posedge Clks_clk) begin
		if( Clks_extReset)
			rFC <= '0;
		else if( enT1 & Nanod_permStart) begin		// S0 phase of bus cycle
			rFC[2] <= pswS;
			// If FC is type 'n' (0) at ucode, access type depends on PC relative mode
			// We don't care about RZ in this case. Those uinstructions with RZ don't start a bus cycle.
			rFC[1] <= microLatch[ 16] | ( ~microLatch[ 15] & Irdecod_isPcRel);
			rFC[0] <= microLatch[ 15] | ( ~microLatch[ 16] & ~Irdecod_isPcRel);
		end
	end


	// IPL interface
	reg [2:0] inl;							// Int level latch
	reg updIll;
	reg prevNmi;

	wire nmi = (iIpl == 3'b111);
	wire iplStable = (iIpl == rIpl);
	wire iplComp = iIpl > pswI;

	always @( posedge Clks_clk) begin
		if( Clks_extReset) begin
			intPend <= 1'b0;
			prevNmi <= 1'b0;
		end
		else begin
			if( Clks_enPhi2)
				prevNmi <= nmi;

			// Originally async RS-Latch on PHI2, followed by a transparent latch on T2
			// Tricky because they might change simultaneously
			// Syncronous on PHI2 is equivalent as long as the output is read on T3!

			// Set on stable & NMI edge or compare
			// Clear on: NMI Iack or (stable & !NMI & !Compare)

			if( Clks_enPhi2) begin
				if( iplStable & ((nmi & ~prevNmi) | iplComp) )
					intPend <= 1'b1;
				else if( ((inl == 3'b111) & Iac) | (iplStable & !nmi & !iplComp) )
					intPend <= 1'b0;
			end
		end

		if( Clks_extReset) begin
			inl <= '1;
			updIll <= 1'b0;
		end
		else if( enT4)
			updIll <= microLatch[0];		// Update on any IRC->IR
		else if( enT1 & updIll)
			inl <= iIpl;					// Timing is correct.

		// Spurious interrupt, BERR on Interrupt Ack.
		// Autovector interrupt. VPA on IACK.
		// Timing is tight. Spuria is deasserted just after exception exception is recorded.
		if( enT4) begin
			Spuria <= ~BeiDelay & Iac;
			Avia <= ~Vpai & Iac;
		end

	end

	assign enErrClk = iAddrErr | iBusErr;
	assign wClk = waitBusCycle | ~BeI | iAddrErr | Err6591;

	// E clock and counter, VMA
	reg [3:0] eCntr;
	reg rVma;

	assign VMAn = rVma;

	// Internal stop just one cycle before E falling edge
	wire xVma = ~rVma & (eCntr == 8);

`ifdef USE_E_CLKEN
	assign E_PosClkEn = (Clks_enPhi2 & (eCntr == 5));
	assign E_NegClkEn = (Clks_enPhi2 & (eCntr == 9));
`endif

	always @( posedge Clks_clk) begin
		if( Clks_pwrUp) begin
			E <= 1'b0;
			eCntr <='0;
			rVma <= 1'b1;
		end
		if( Clks_enPhi2) begin
			if( eCntr == 9)
				E <= 1'b0;
			else if( eCntr == 5)
				E <= 1'b1;

			if( eCntr == 9)
				eCntr <= '0;
			else
				eCntr <= eCntr + 1'b1;
		end

		if( Clks_enPhi2 & addrOe & ~Vpai & (eCntr == 3))
			rVma <= 1'b0;
		else if( Clks_enPhi1 & eCntr == '0)
			rVma <= 1'b1;
	end

	always @( posedge Clks_clk) begin

		// This timing is critical to stop the clock phases at the exact point on bus/addr error.
		// Timing should be such that current ublock completes (up to T3 or T4).
		// But T1 for the next ublock shouldn't happen. Next T1 only after resetting ucode and ncode latches.

		if( Clks_extReset)
			rAddrErr <= 1'b0;
		else if( Clks_enPhi1) begin
			if( busAddrErr & addrOe)		// Not on T1 ?!
				rAddrErr <= 1'b1;
			else if( ~addrOe)				// Actually async reset!
				rAddrErr <= 1'b0;
		end

		if( Clks_extReset)
			iBusErr <= 1'b0;
		else if( Clks_enPhi1) begin
			iBusErr <= ( BerrA & ~BeI & ~Iac & !BusRetry);
		end

		if( Clks_extReset)
			BerrA <= 1'b0;
		else if( Clks_enPhi2) begin
			if( ~BeI & ~Iac & addrOe)
				BerrA <= 1'b1;
			// else if( BeI & addrOe)			// Bad, async reset since addrOe raising edge
			else if( BeI & busStarting)			// So replaced with this that raises one cycle earlier
				BerrA <= 1'b0;
		end

		// Signal reset exception to sequencer.
		// Originally cleared on 1st T2 after permstart. Must keep it until TVN latched.
		if( Clks_extReset)
			excRst <= 1'b1;
		else if( enT2 & Nanod_permStart)
			excRst <= 1'b0;

		if( Clks_extReset)
			A0Err <= 1'b1;								// A0 Reset
		else if( enT3)									// Keep set until new urom words are being latched
			A0Err <= 1'b0;
		else if( Clks_enPhi1 & enErrClk & (busAddrErr | BerrA))		// Check bus error timing
			A0Err <= 1'b1;

		if( Clks_extReset) begin
			iStop <= 1'b0;
			Err6591 <= 1'b0;
		end
		else if( Clks_enPhi1)
			Err6591 <= enErrClk;
		else if( Clks_enPhi2)
			iStop <= xVma | (Vpai & (iAddrErr | ~rBerr));
	end

	// PSW
	logic irdToCcr_t4;
	always @( posedge Clks_clk) begin
		if( Clks_pwrUp) begin
			Tpend <= 1'b0;
			{pswT, pswS, pswI } <= '0;
			irdToCcr_t4 <= '0;
		end

		else if( enT4) begin
			irdToCcr_t4 <= Irdecod_toCcr;
		end

		else if( enT3) begin

			// UNIQUE IF !!
			if( Nanod_updTpend)
				Tpend <= pswT;
			else if( Nanod_clrTpend)
				Tpend <= 1'b0;

			// UNIQUE IF !!
			if( Nanod_ftu2Sr & !irdToCcr_t4)
				{pswT, pswS, pswI } <= { ftu[ 15], ftu[13], ftu[10:8]};
			else begin
				if( Nanod_initST) begin
					pswS <= 1'b1;
					pswT <= 1'b0;
				end
				if( Nanod_inl2psw)
					pswI <= inl;
			end

		end
	end

	// FTU
	reg [4:0] ssw;
	reg [3:0] tvnLatch;
	logic [15:0] tvnMux;
	reg inExcept01;

	// Seems CPU has a buglet here.
	// Flagging group 0 exceptions from TVN might not work because some bus cycles happen before TVN is updated.
	// But doesn't matter because a group 0 exception inside another one will halt the CPU anyway and won't save the SSW.

	always @( posedge Clks_clk) begin

		// Updated at the start of the exception ucode
		if( Nanod_updSsw & enT3) begin
			ssw <= { ~bciWrite, inExcept01, rFC};
		end

		// Update TVN on T1 & IR=>IRD
		if( enT1 & Nanod_Ir2Ird) begin
			tvnLatch <= tvn;
			inExcept01 <= (tvn != 1);
		end

		if( Clks_pwrUp)
			ftu <= '0;
		else if( enT3) begin
			case( 1'b1)
			Nanod_tvn2Ftu:				ftu <= tvnMux;

			// 0 on unused bits seem to come from ftuConst PLA previously clearing FBUS
			Nanod_sr2Ftu:				ftu <= {pswT, 1'b0, pswS, 2'b00, pswI, 3'b000, ccr[4:0] };

			Nanod_ird2Ftu:				ftu <= Ird;
			Nanod_ssw2Ftu:				ftu[4:0] <= ssw;						// Undoc. Other bits must be preserved from IRD saved above!
			Nanod_pswIToFtu:			ftu <= { 12'hFFF, pswI, 1'b0};			// Interrupt level shifted
			Nanod_const2Ftu:			ftu <= Irdecod_ftuConst;
			Nanod_abl2Pren:				ftu <= Abl;								// From ALU or datareg. Used for SR modify
			default:					ftu <= ftu;
			endcase
		end
	end

	always @* begin
		if( inExcept01) begin
			// Unique IF !!!
			if( tvnLatch == TVN_SPURIOUS)
				tvnMux = {9'b0, 5'd24, 2'b00};
			else if( tvnLatch == TVN_AUTOVEC)
				tvnMux = {9'b0, 2'b11, pswI, 2'b00};				// Set TVN PLA decoder
			else if( tvnLatch == TVN_INTERRUPT)
				tvnMux = {6'b0, Ird[7:0], 2'b00};					// Interrupt vector was read and transferred to IRD
			else
				tvnMux = {10'b0, tvnLatch, 2'b00};
		end
		else
			tvnMux = { 8'h0, Irdecod_macroTvn, 2'b00};
	end

endmodule
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
